Panda-Intelligence/panda-standard-board/hardware/thin18-compact/c4d9-96x68-aip-buffers/README.md

# Thin18 Compact C4D-9 — AIP74LVC2G17 EPD buffers

U801-U803 are changed to Wuxi I-core AIP74LVC2G17GC363.TR / C3294722 using the existing SOT-363 footprints and identical nets. Native ERC/DRC/parity are clean. Threshold/leakage/waveform qualification remains open.
