Panda-Intelligence/panda-standard-board/hardware/thin18-compact/core-c1-96x68-split/eda/core/PANDA-STD-CORE-EVT/PANDA-THIN16/models/README.md

# USB4500 model restoration

The STEP is the pinned KiCad Tiny Tapeout demo asset, Git blob
`cee214252a14ce383e84d3eaf1a94ca5bc54bab2`. Restore with the source tool
`restore_thin13_model.py`; the local delivery package includes it.
The donor demo licence is Apache-2.0 (LICENSE.txt). The model is a reference,
not independent manufacturer or worst-case tolerance approval.
