Panda-Intelligence/panda-standard-board/docs/design/key-calculations.md

# Panda 標準電子書板：WP4 關鍵計算清單

工作包：WP4（EVT 核心板原理圖）
日期：2026-08-11（USB／IRQ／BQ_PG差量同步：2026-09-08，Codex）
狀態：數據手冊計算 + 已提升USB／IRQ／BQ_PG工程候選；**不等於資格完成**。WP3官方模型／原廠EVM或受控bench仍無完整結論，WP3／WP4 pass與製造發布保持未關閉；保留`VFB`容差及§5／§6歷史取捨
適用板號：`PANDA-STD-CORE-EVT`

本文件承接 [power-datasheet-calculations.md](power-datasheet-calculations.md)（WP3）的 §12 傳遞項，補完
WP4 必辦計算，並新增充電輸入限流、超級電容與擴充器終端三項 WP4 專屬計算。凡 WP3 已算過者只作交叉引用與
必要重算，不重複抓取數據手冊。

2026-09-08 正式USB／IRQ／BQ_PG工程候選已提升（149封裝／1766段／306via，DRC0/0/0、ERC18）；共同證據見
[USB2 S-9 A-stage](lib/review/USB2-S9-A-stage.md)與[BQ_PG記錄](lib/review/BQ_PG-P10-A-stage.md)。本輪只同步相關差量；8月計算與取捨保留為歷史，
深睡還須計入未有界的PG專屬漏電；既有混合包絡見§4.5、總USB源電流門見§5.3.1，不以CAD檢查代替任何製造／台架資格。

---

## 0. 標記與新增假設

| 標記 | 意義 |
| --- | --- |
| **[手]** | 官方數據手冊值，可在文件號對應章節複核 |
| **[算]** | 由 **[手]** 值依本文件列出的算式推算 |
| **[估]** | 估算／規劃假設，未經實測，**不得**作為承諾 |

沿用 WP3 §0.1 的壓力情境 A1–A5（3.0／4.2 V 只作 TPS63802 VIN 情境，不是 `VSYS_RAW` rail bounds；
η=0.90、負載 0.70／1.00 A、f=1.4 MHz）。本文件新增：

| # | 假設 | 值 | 為何是假設 | 解除條件 |
| --- | --- | --- | --- | --- |
| A6 | 超級電容自漏電流 | **[估]** 1／5／10 µA 三檔並列 | 精確料號未選定；漏電是超級電容最大變異項，且與容量正相關 | WP4 選型取得25 °C／實際施加電壓下漏電及調理時間；額定電壓測試另列 |
| A7 | `VSYS_RAW` qualification bounds | **未凍結；4.5 V 僅作元件壓力點** | `SYS` 依 `VSYSMIN`、`VBAT`、source mode、system／charge load、DPM／thermal regulation、BATFET 與 dropout；不得先宣稱 fixed max | WP3 受控計算 + 官方模型模擬或 EVM／bench fallback |
| A8 | 快充目標輸入電流 | **[算]** 約 0.93 A + 系統併載 | 由 1 A 電池充電、4.2 V 電芯、5 V 輸入、η=0.90 推算 | 目標電芯與整機熱資格 |

---

## 1. `3V3_AON` 反饋分壓完整誤差（補齊 WP3 §5.4 缺失輸入）

### 1.1 補轉錄的 `VFB` 容差與模式邊界

WP3 §5.4 標記 `VFB` 容差**未轉錄**，導致 §5.3 誤差窗口不完整。WP4 已從 SLUSEB5B 電氣特性表補轉錄：

| 符號 | 參數 | 測試條件 | MIN | TYP | MAX | 單位 |
| --- | --- | --- | --- | --- | --- | --- |
| `VFB` | Feedback Regulation Voltage | — | — | 500 | — | mV |
| `VFB` | **Feedback Voltage accuracy** | **PWM mode** | **−1** | — | **+1** | **%** |
| `IFB` | Feedback Input Bias Current | VFB = 500 mV | — | 5 | 100 | nA |
| `VTHR;EN` | EN 腳上升門檻 | — | 1.07 | 1.1 | 1.13 | V |
| `VIH` | 高電平輸入電壓 | — | 1.2 | — | — | V |
| `VIL` | 低電平輸入電壓 | — | — | — | 0.4 | V |
| `tPG;delay` | Power Good 延遲 | `VFB` 下降 | — | 14 | — | µs |

⚠ **`VFB` 容差只在 PWM mode 下規範。** `IPWM/PFM` 1.06 A 的完整定義是「進入 PFM 的峰值電感電流」，
不是輸出負載電流。WP3 舊版把 0.70／1.00 A `IOUT` 直接與 1.06 A 比較，據此斷言全部正常負載為 PFM；
該推論已撤回。下列窗口只表示**資料手冊 PWM 條件**，不能套用到尚未判定模式的 automatic PWM/PFM 工作點，
也不能證明 PFM 直流精度。

### 1.2 PWM 規範條件下的三項疊加重算 **[算]**

```text
VOUT = VFB × (1 + R1/R2) + IFB × R1
```

R1 = 560 kΩ、R2 = 100 kΩ（WP3 §5.1 選項 F1，R2 為數據手冊上限 **[手]**）。

最壞高側：`VFB` 取 505 mV、R1 取上限、R2 取下限、`IFB` 取 100 nA
最壞低側：`VFB` 取 495 mV、R1 取下限、R2 取上限、`IFB` 取 0

| 電阻容差 | VOUT 最壞低 **[算]** | VOUT 最壞高 **[算]** | 對 3.6 V 上界餘裕 | 對 3.0 V 下界餘裕 |
| --- | --- | --- | --- | --- |
| ±1 % | 3.2076 V | **3.4467 V** | 0.1533 V | 0.2076 V |
| **±0.5 %（採用）** | **3.2394 V** | **3.4177 V** | **0.1823 V** | **0.2394 V** |
| ±0.25 % | 3.2554 V | 3.4033 V | 0.1967 V | 0.2554 V |

±0.5 % 的逐步代入 **[算]**：

```text
高側：R1 = 562.8 kΩ、R2 = 99.5 kΩ → R1/R2 = 5.656281 → (1+R1/R2) = 6.656281
      VFB 項 = 0.505 × 6.656281      = 3.361422 V
      IFB 項 = 100 nA × 562.8 kΩ     = 0.056280 V
      VOUT_max                       = 3.417702 V

低側：R1 = 557.2 kΩ、R2 = 100.5 kΩ → R1/R2 = 5.544279 → (1+R1/R2) = 6.544279
      VOUT_min = 0.495 × 6.544279    = 3.239418 V
```

### 1.3 與 WP3 §5.3 的差異與後果

| 項目 | WP3 §5.3（未含 `VFB` 容差） | WP4 本節（含 `VFB` ±1 %） | 變化 |
| --- | --- | --- | --- |
| VOUT 窗口（±0.5 %） | 3.2721 … 3.3844 V | **3.2394 … 3.4177 V** | 擴大 0.0663 V |
| 上側紋波預算 | 0.216 V | **0.1823 V** | **−15.6 %** |
| 下側紋波預算 | 0.272 V | **0.2394 V** | −12.0 % |

比對基準 **[手]**：ESP32-S3 `VDD3P3`／`VDD3P3_RTC`／`VDD3P3_CPU` 建議 3.0／3.3／3.6 V。

**判定：在 PWM 規範條件下，加入 `VFB` 容差後窗口仍完整落在 3.0–3.6 V 內，±0.5 % 電阻選擇可作 EVT
候選。** 0.1823 V／0.2394 V 只是該 PWM 算術窗口到絕對電壓邊界的距離；因 `VFB` accuracy 未規範 PFM，
**不得**把這兩個數字當 automatic/PFM 紋波預算或資格門。

不建議僅為增加 PWM 算術距離改用 ±0.25 % 電阻。正確關門方式是以 `MODE`=LOW／HIGH 分別掃 VIN、負載與
Wi-Fi/SD 工況，直接確認 `VOUT` 全時域維持 3.0–3.6 V；活動態 `MODE` 策略在該實測前保持未凍結。

### 1.4 分壓靜態電流（併入 §4）

```text
Idiv = VOUT / (R1 + R2) = 3.3 / 660 kΩ = 5.00 µA   [算]
```

R2 ≤ 100 kΩ 是數據手冊硬上限 **[手]**，故 5.00 µA 是此拓樸的**數學下限**（WP3 §7.2 已證），本文件沿用。

---

## 2. XFL4015 family reference candidate 峰值電流與飽和裕度情境（C2 後重算）

### 2.1 C2 決策的電感有效值窗口

WP3 §4.3 衝突一採 **C2：±20 %（或更緊）容差的 0.47 µH**，使有效值 **0.376–0.564 µH** 完整落入數據手冊建議
工作條件 0.37–0.57 µH **[手]**。IPEAK 的紋波項與 L 成反比，故最壞條件為 **L = 0.376 µH**。

### 2.2 式 (2) 代入（VIN = 3.0 V boost 壓力情境；不是已知最惡劣 rail bound） **[算]**

```text
IPEAK = Iout / (η × (1 − D))  +  (Vin × D) / (2 × f × L)
D = 0.0909、η = 0.90、f = 1.4 MHz、L = 0.376 µH

紋波項 = (3.0 × 0.0909) / (2 × 1.4e6 × 0.376e-6) = 0.2727 / 1.0528 = 0.2590 A
```

| Iout | DC 項 **[算]** | 紋波項 **[算]** | **IPEAK** **[算]** | ×1.2 數據手冊建議裕度 **[手]** |
| --- | --- | --- | --- | --- |
| 0.70 A **[假 A3]** | 0.8556 A | 0.2590 A | **1.1146 A** | 1.3375 A |
| 1.00 A **[假 A4]** | 1.2222 A | 0.2590 A | **1.4812 A** | 1.7774 A |
| 2.00 A 數據手冊上限 | 2.4444 A | 0.2590 A | **2.7034 A** | 3.2441 A |

### 2.3 對 TI 推薦表所列 Isat 5.4 A 與 `IPK` MIN 4 A 的情境裕度 **[算]**

| Iout | ×1.2 值 | vs Isat 5.4 A **[手]** | IPEAK | vs `IPK` MIN 4 A **[手]** |
| --- | --- | --- | --- | --- |
| 0.70 A | 1.3375 A | **4.04×** | 1.1146 A | **3.59×** |
| 1.00 A | 1.7774 A | **3.04×** | 1.4812 A | **2.70×** |
| 2.00 A | 3.2441 A | **1.66×** | 2.7034 A | **1.48×** |

**判定：C2 選定的 ±20 % 容差件在全負載範圍對 Isat 與 IC 限流都有裕度，無衝突。**
且 C2 比 WP3 表中用 −30 % 降額（L=0.329 µH、紋波 0.296 A）更寬鬆，證實 C2 是收緊而非放寬。

⚠ 沿用 WP3 §4.4 的殘留風險：Isat 5.4 A < `IPK` MAX 5.75 A **[手]**，故障暫態下電感可能先於 IC 限流飽和。
本節不改變該風險評級（已知殘留、非阻塞、列故障注入台架項）。

### 2.4 WP4 選型必辦（尚未關閉）

C2 只凍結**電氣容差要求**，不等於 TI 推薦表中的 `XFL4015-471ME` exact name 已合格。必辦：

1. 由供應商確認 exact suffix／orderable MPN 與 reel／packaging；
2. 取得該可訂購料號的**容差規格**，確認為 ±20 % 或更緊；
3. 取得**電流／溫度降額曲線**，確認在 §2.2 壓力情境與工作溫度下有效值仍 ≥0.37 µH；
4. 確認供應商的**飽和定義**與 supplier-controlled land pattern。

XFL4015 family body envelope 為 **4.0×4.0×1.5 mm**，但這不凍結 land pattern。**推薦表本身不構成上述任一項
驗證。** 全部資料取得前 `L401` 只可視為 family／reference candidate。

---

## 3. 有效電容降額驗算

數據手冊建議工作條件為**有效值** **[手]**；降額假設為電容 **+20 % / −50 %** **[手]**。

| 位置 | 數據手冊 MIN（有效） | 標稱 | 最壞降額有效值 **[算]** | 裕度 **[算]** | 判定 |
| --- | --- | --- | --- | --- | --- |
| `CO`（VOUT） | **7 µF** | 22 µF 單顆 | 11.0 µF | **1.57×** | ✅ |
| `CI`（VIN） | **4 µF** | 10 µF | 5.0 µF | **1.25×** | ⚠ 偏緊 |
| `CI`（若採 E2） | 4 µF | 22 µF | 11.0 µF | **2.75×** | ✅ |

### 3.1 `CI` 取捨結論：採 WP3 §8.2 的 E2

WP3 §8.2 列出 E1／E2／E3 三選項並未裁決。WP4 **採 E2：`CI` 改 22 µF / 6.3 V**，理由：

| 理由 | 說明 |
| --- | --- |
| 裕度由 1.25× 升至 2.75× | −50 % 是**通用**降額假設，未含本設計實際 DC bias、溫度與老化三項疊加 |
| DC bias 壓力條件 | `VSYS_RAW` 上界未凍結；4.5 V 只作 **[假 A7]** 壓力點。6.3 V 0603 X5R 在高偏置下容值跌落**可能超過 50 %**，須以 WP3 受控 max 重算 |
| 數據手冊明許 | 「輸入電容值可無限制增加」**[手]** |
| 佔位與成本代價低 | 同 0603 封裝，僅成本略增；ESR 維持 10 mΩ（不像 E1 升到 40 mΩ） |
| 組合合法性不變 | 0.47 µH + 10 µF 的非法組合限制**只針對 `CO`**（WP3 §8.1），`CI` 不受該表約束 |

**採 E2 後 §3 全部項目都有 ≥1.57× 裕度，`CI` 不再是最緊項。** 但 DC bias 曲線驗證**仍必辦**：E2 降低風險，
不消除驗證義務。

⚠ 原理圖與複核清單必須明確標注 `CI` 與 `CO` 的組合限制區分（WP3 §8.1 已警告此為易誤讀點），避免複核者
把 `CI` 判為非法組合。

### 3.2 bulk 電容判定

數據手冊 **[手]**：輸入源距 IC 超過數英寸需追加 bulk 電容（典型 47 µF 電解／鉭）。
`VSYS_RAW` 來自同板 BQ25628E，距離短 → **預期不需要**。此判定須在 WP7A 實際佈局距離確定後複核（WP3 §12 已列）。

---

## 4. 深睡靜態電流最終表（D1 決策後）

本表保留8月器件預算基線，僅USB／IRQ相關行加入當前覆蓋，不重新資格化其他器件；§4.2–4.3舊合計為
USB監控加入前的歷史推導，當前差量覆蓋見§4.5。

### 4.1 逐元件表

| 元件 | 狀態 | typ | max | 依據 |
| --- | --- | --- | --- | --- |
| ESP32-S3 | Deep-sleep，RTC memory + RTC 週邊上電 | **8.0 µA** | — | 晶片規格書 v2.2 表 5-10 **[手]** |
| TPS63802 | power save（`MODE`=LOW）、輕載 | **11 µA** | — | SLVSEU9D Iq **[手]** |
| BQ27427 | **SLEEP**（D1 已決策保留） | **9.0 µA** | — | SLUSEB5B §5.5 `ISLP` **[手]** |
| BQ25628E | battery-only、BATFET 開、**ADC 關** | **1.5 µA** | 3 µA | SLUSFA4C `IQ_BAT` **[手]** |
| TUSB320LI | VBUS-only，拔線後無主動電池供電；隔離／監控有限負載另列 | — | — | 非整接口零負載；S-9掉電／漏電仍待測 |
| USB隔離／監控 | 指定稳態工程預算 **3.8µA**，非typ/max器件規格 | — | — | §4.5條件假設；半掉電／ramp不在此保證 |
| TCA9535 #1 | standby、`fSCL`=0、no load | **0.9 µA** | 2.2／4 µA | SCPS201E（見 §4.3） **[手]** |
| RV-3028-C7 | 切換停用的歷史timekeeping例；I²C inactive、CLKOUT disabled、VDD=3 V/25°C、I/O在0或VDD | **0.045 µA** | 0.060 µA | 手冊p97 `IDD`（舊稿稱IDDO）；未來啟用LSM須改核`IDD:LSM`，不能沿用此列 |
| **`3V3_AON` FB 分壓** | 恆導通 | **5.00 µA** | — | §1.4 **[算]**（WP3 §7.1 首次發現） |
| **超級電容自漏電** | 涓流充飽後由 `3V3_AON` 持續補償 | **[估] 1–10 µA** | — | **§6 新發現，power-tree.md §5 未列** |
| LSM6DSO32X | power-down | **待實測** | — | 需按實際 ODR／量程複核 |
| 負載開關 ×4 | 關斷漏電 | **[估] <1 µA 合計** | — | 料號未定 |
| I²C／INT／KEY_POWER_MCU上拉 | 空閒高時理想電阻無壓差，接收器漏電仍計入 | ≈0（僅電阻本體） | — | §7.1，非整接口零負載 |
| TCA9535 P15備用終接 | 保留100k下拉；P16/P17為10k AON上拉CC輸入 | ≈0（僅P15電阻本體） | — | §7.3當前覆蓋 |
| BQ_PG／P10上拉 | R600=10k／1%至AON；battery-only釋放高態的PG專屬漏電未定 | 待驗 | 待驗 | 不能借INT/STAT界限；有效输入低態約0.33mA是另一供電狀態的電阻計算 |
| TUSB320 `EN_N` 網路 | 固定接GND；VBUS=0無本地上拉供電 | — | — | VBUS有效時耗流屬USB域，不能用舊「靠內部上拉停用」描述本候選 |
| MAX98357A `SD_MODE` 分壓 | `VSYS_AUDIO` 關斷 → 分壓源為 0 | **0** | — | §7.3 |

### 4.2 歷史合計與判定（USB監控加入前） **[算]**

```text
已知固定項（不含超級電容、IMU、開關漏電）：
  8.0 + 11 + 9.0 + 1.5 + 0 + 0.9 + 0.045 + 5.00 = 35.445 µA

+ 超級電容漏電 1 µA  [估]  → 36.45 µA
+ 超級電容漏電 5 µA  [估]  → 40.45 µA
+ 超級電容漏電 10 µA [估]  → 45.45 µA
```

| 情境 | 合計 **[算]** | vs 50 µA 上限（D1 基準） | 餘裕 |
| --- | --- | --- | --- |
| 超級電容漏電 1 µA | 36.45 µA | 計算包絡內 | **13.55 µA** |
| 超級電容漏電 5 µA | 40.45 µA | 計算包絡內 | **9.55 µA** |
| 超級電容漏電 10 µA | 45.45 µA | 偏緊 | **4.55 µA** |

**上述餘裕尚須容納 LSM6DSO32X power-down 與 4 顆負載開關漏電（合計 <1 µA **[估]**）。**

### 4.3 ⚠ 歷史：對 D1「餘 13.60 µA」的修正

D1 決策記錄曾稱「50 µA 上限仍餘 13.60 µA」，但漏了超級電容；上一版又錯把 VBUS-only TUSB320LI 的
1.7 µA shutdown max 加入電池深睡。兩項一併修正後，採 S1 漏電 1–5 µA 時的計算餘裕為 **9.55–13.55 µA**。

**這不推翻 D1，也不構成通過**：IMU power-down、四顆負載開關、板面污染與溫度仍未實測。超級電容漏電仍是
關鍵選型參數；10 µA 級只餘 4.55 µA，不得在其餘漏電未知時採用。

→ **超級電容選型準則S1：25 °C、實際施加電壓下漏電 ≤5 µA**（見 §6.4）；額定電壓或不同調理時間的資料不得混同。

### 4.4 ✅ 反面查核：TCA9535 standby 測試條件（關閉 WP3 §7.4 疑慮）

WP3 §7.4 標記「0.9 µA typ 的測試條件（VCC=3.6 V、輸入接地）與本設計實際狀態不符」，因本設計深睡時多路
擴充器輸入為 HIGH。WP4 回查 SCPS201E 電氣特性表，發現數據手冊給出**兩組**測試條件：

| 測試條件 | VCC | typ | max |
| --- | --- | --- | --- |
| **VI = VCC**（輸入全高）、IO = 0、I/O = inputs、`fSCL` = 0 kHz、no load | 3.6 V | **0.9 µA** | **2.2 µA** |
| **VI = GND**（輸入全低）、IO = 0、I/O = inputs、`fSCL` = 0 kHz、no load | 3.6 V | **0.9 µA** | **4 µA** |

**兩個包絡條件的 typ 都是 0.9 µA。** 本設計輸入為高低混合，必然落在兩者之間。

**判定：WP3 §7.4 的疑慮解除。0.9 µA typ 適用；max 以較差者 4 µA 為界。**
⚠ 但兩列條件都註明 `I/O = inputs`，而本設計 P00–P03／P05 為**輸出**（當前P10已保留輸入）。深睡時這些輸出的電位已在
§7.2／§7.3 逐一確認為不產生電流，故仍適用；WP9 實測依舊必要（power-tree.md §5 已列）。

**來源編號更正已同步**：舊版曾誤記 TCA9535 文件號。官方下載文件頁眉為
**SCPS201E – AUGUST 2009 – REVISED MAY 2022**；目前受控文件一律使用 SCPS201E。此更正不改變電氣結論。

### 4.5 2026-09-08 USB差量包絡（不是整板max保證）

條件為VBUS=0、AON有效、CC rail已穩定放電：AUP2G07雙路保守2.4µA + AUP1G17輸入0.5µA + ICC0.9µA =
**3.8µA**。2.4µA含Ioff與ΔIoff保守相加假設，不是廠家全狀態新保證；0.2–0.8V及ramp另測。
47k+1%=47.47k泄放在2.9µA假設注入下約0.1377V，不能據此證明全衰減過程受控。

```text
舊已知typ／估算固定項35.445µA + USB指定穩態预算3.8µA = 39.245µA
+ 超級電容估算1 / 5 / 10µA → 40.245 / 44.245 / 49.245µA
對50µA名義餘量             →  9.755 /  5.755 /  0.755µA
```

採1–5µA超級電容假設，當前混合工程包絡四捨五入 **40.25–44.25µA**，餘量 **5.75–9.75µA**。
這混合typ、估算與部分保守器件預算，**不是整板最壞電流，也未通過50µA門**。超級電容尚未實現，
IMU、開關、板漏、溫度、實際DC狀態和過渡仍未完成。不得把舊舍入數重複累加或將3.8µA當typ規格。

---

## 5. 🔴 新衝突一：500 mA 硬體默認與 1 A 電池充電互斥

### 5.1 BQ25628E 輸入限流的兩個來源

| 來源 | 機制 | POR 預設 | 復位條件 | 依據（SLUSFA4C **[手]**） |
| --- | --- | --- | --- | --- |
| `ILIM` 腳（硬體） | `IINREG = KILIM / RILIM`，`RILIM` 接地 | 由電阻決定，**與韌體無關** | 不適用（硬體） | §6 腳位表、§7.5 |
| `IINDPM` 暫存器（韌體） | REG0x06/07 | **3200 mA（A0h）** | `REG_RESET`；**移除轉接器時重置回 3.2 A** | REG0x06 欄位表 |
| `EN_EXTILIM` | =0 時**停用 `ILIM` 腳** | **1h（啟用）** | `REG_RESET`、**`WATCHDOG`** | REG0x15 bit 2 |
| `ICHG`（電池充電電流） | REG0x02/03 | **320 mA（8h）**，範圍 40–2000 mA | `REG_RESET`；watchdog 逾時設為前值 **1/2** | REG0x02 欄位表 |

實際輸入限流 = `ILIM` 腳與 `IINDPM` **兩者取小** **[手]**。

### 5.2 ⚠ 關鍵推論：`IINDPM` 無法提供安全默認

`IINDPM` 的 POR 值是 **3200 mA**，且**移除轉接器時自動重置回 3.2 A**。因此：

> PRD 的默認≤500mA總門不能靠暫存器POR值關閉；BQ分支須由`ILIM`電阻提供默認限制，另須給繞過BQ的USB旁路留出預算。

這使 `RILIM` 從「可選的額外保護」升級為**必裝且不可省的安全元件**。既有文件（power-tree.md §7、
i2c-address-map.md）未記錄 `ILIM` 腳與 `RILIM`，WP4 於此補齊並列為原理圖必辦項。

### 5.3 `RILIM` 計算（500 mA 硬體默認） **[算]**

`KILIM` = 2250 / 2500 / 2750 AΩ（MIN/TYP/MAX，測試條件 **INREG = 1.6 A**） **[手]**。
最壞高電流 = `KILIM` 取 MAX、`RILIM` 取下限：

```text
RILIM_min ≥ KILIM_max / 0.5 A = 2750 / 0.5 = 5500 Ω
E24 取 5.6 kΩ ±1 % → 5544 … 5656 Ω

IINREG 外推高 = 2750 / 5544 = 0.4960 A   （僅BQ分支，不是總USB門通過）
IINREG 最壞低 = 2250 / 5656 = 0.3979 A
→ 輸入限流窗口 398 … 496 mA
```

**判定邊界：5.6 kΩ ±1 % 產生 398–496 mA 是把 `KILIM` 的 1.6 A 規範外推到 0.4–0.5 A 的計算窗口，
不是資料手冊保證窗口，也不能單憑此式宣稱 PRD 硬體默認已合格。**

此外，SLUSFA4C §8.3.3.3 明文要求：ILIM 設定**低於 400 mA**時，須在 `RILIM` 並聯一條 **1.2 kΩ + 330 nF
串聯 RC** 支路。計算窗口低端 397.9 mA 已跨過 400 mA，因此 EVT 原理圖必須裝此 RC；缺任一元件即阻塞
輸入限流門。WP9須在J201量測上電、穩態、拔插、弱源與溫度下的**總源電流**，含全部旁路，≤500mA才可關門。

### 5.3.1 2026-09-08 總USB源電流邊界（仍未通過）

```text
I_USB_source = I_BQ_input + I_R209 + I_LDO_input + I_VBUS_divider + I_TUSB_VBUS_DET + 其他入口漏電／動態充電
I_R209(5.5V, -1%) = 5.5V / 990Ω = 5.5556mA
R209功耗 = 5.5² / 990Ω = 30.5556mW（0603，要求≥0.1W）
原KILIM外推上端 = 2750 / 5544 = 496.0317mA（僅BQ分支，且非此工作點保證規格）
只相加上述兩項 = 501.5873mA，尚未計CC／LDO／monitor
```

此式證明**原預算不足以關閉總門**，不表示任意實板必然一直超500mA。本輪不改R201，不能只把BQ支路設為500mA
就宣稱整機合格。CC rail內47k泄放約70.2µA、4.7k OUT1/2低態各約0.702mA、OUTA上拉／下拉及IC耗流屬
`I_LDO_input`的內部分解，不能再在LDO輸入之外重複相加。較高CC源能力也須連同電芯／NTC／熱與總源預算實測。

直接VBUS電容C202/C209各1µF，共2µF nominal；CC rail C210=2.2µF與C211/C212/C213各0.1µF，共2.5µF。
六顆4.5µF，統一+20%=5.4µF，按5.5V為29.7µC；非全系統inrush保證，C215/TVS寄生、BQ啟動至PMID/SYS及
實際插拔仍待測。C214屬AON不重複加；C210的exact MPN須在3.3V、全容差／溫度／DC-bias後有效≥1.5µF。

### 5.4 衝突：1 A 電池充電需要約 2 倍於該上限的輸入電流 **[算]**

```text
電池側功率  = 1.0 A × 4.2 V              = 4.20 W
輸入側功率  = 4.20 / 0.90 [假 A2]        = 4.67 W
5 V 輸入電流 = 4.67 / 5                   = 0.933 A   [假 A8]
再加系統併載（MCU + SD + 顯示邏輯）      → 更高
```

反推：在 `ILIM` 固定 5.6 kΩ、`EN_EXTILIM`=1 的條件下可達的最大電池充電電流：

| 輸入限流 | 輸入功率 | ×0.90 | @4.2 V 電芯 | @3.7 V 電芯 |
| --- | --- | --- | --- | --- |
| 0.398 A（最壞低） | 1.99 W | 1.79 W | **0.426 A** | 0.484 A |
| 0.496 A（最壞高） | 2.48 W | 2.23 W | **0.531 A** | 0.604 A |

**且上表尚未扣除系統併載。**

> 🔴 **衝突：`RILIM` 若恆定為 500 mA 級，電池充電電流上限約 0.43–0.60 A，PRD 已凍結的「最高 1 A 電池充電」
> 在物理上不可達。**

### 5.5 歷史L1／L3取捨選項（當前總源門由§5.3.1覆蓋）

| 選項 | 作法 | 優點 | 代價／風險 | 判定 |
| --- | --- | --- | --- | --- |
| **L1** | `RILIM` = 5.6 kΩ 恆在；資格通過後韌體寫 `EN_EXTILIM`=0 **停用 `ILIM` 腳**，改由 `IINDPM` 控制 | 零額外元件；POR為BQ分支500mA級外推候選，非總源門通過；WATCHDOG可恢復EN_EXTILIM=1 | 快充期間硬體夾制**不存在**；見§5.6拔插風險與§5.3.1總源門 | 歷史EVT基線，資格未關 |
| L2 | `RILIM` 直接按快充上限（1.2 A → 2.32 kΩ）設定，500 mA 默認交由韌體寫 `IINDPM` | 硬體夾制恆在且無需切換 | ❌ `IINDPM` POR = 3.2 A，POR 到韌體寫入之間有最高約 1.2 A 的開窗；**違反 PRD 硬體默認要求** | ❌ 不採 |
| **L3** | `RILIM` = 5.6 kΩ 恆在，並聯一顆 4.02 kΩ 經 MOSFET 由擴充器 P15 切入；閘極下拉 → 預設關斷 | 硬體夾制不消失，可刻意抬升約0.96–1.17A；POR仍只是BQ分支500mA級外推 | +1 MOSFET/+1電阻、佔P15；切回需韌體紀律 | 歷史DNP退路；本批未新增此電路，P15仍預留 |

L3 併聯值 **[算]**：

```text
目標快充上限約 1.2 A → R_par ≥ 2750 / 1.2 = 2292 Ω
5.6 kΩ ∥ Rx = 2292 → Rx ≈ 3880 Ω → E96 取 4.02 kΩ ±1 %

最壞低 R_par = 5544 ∥ 4060 = 2343.7 Ω → IINREG 最壞高 = 2750 / 2343.7 = 1.173 A
最壞高 R_par = 5656 ∥ 3980 = 2336.3 Ω → IINREG 最壞低 = 2250 / 2336.3 = 0.963 A
→ 快充輸入窗口 0.963 … 1.173 A（≥0.933 A 需求 ✅）
```

### 5.6 ⚠ L1 的拔插不對稱風險（必須寫入韌體契約與 WP9 測試）

對照 §5.1 的復位條件表：

| 暫存器／位 | 移除轉接器時是否復位 |
| --- | --- |
| `IINDPM` | **是**，重置回 3.2 A **[手]** |
| `EN_EXTILIM` | **否**（只由 `REG_RESET` 與 `WATCHDOG` 復位） **[手]** |

危險序列：

```text
1. 接上合格 1.5 A 源 → 韌體寫 EN_EXTILIM=0、IINDPM=1.2 A → 快充
2. 使用者拔線          → IINDPM 自動重置 3.2 A；EN_EXTILIM 仍為 0（ILIM 腳仍停用）
3. 立即插入弱 500 mA 源 → 硬體夾制不存在、IINDPM=3.2 A
                        → 在韌體重新偵測並改寫前，充電器可能嘗試遠超源端能力的輸入電流
```

`VINDPM`（輸入電壓 DPM）會依 VBUS 塌陷回折電流，這是設計內的保護；但**開窗真實存在**。

**韌體契約（硬體通過的必要條件）**：

1. `EN_EXTILIM`=1 是**靜止狀態**。只有在「GPIO2有效 + TUSB320LI初始化／CC狀態穩定 + 電芯／NTC／熱及總源預算合格」
   全部成立期間才可置 0；
2. GPIO2下降直接撤銷USB／快充資格，合併CC／charger事件後**立即**恢復`EN_EXTILIM=1`並核限流；不能只靠TCA輪詢／EXP_INT。GPIO响应不证明模拟3ms或ROM階段已受控；
3. 充電器 watchdog **必須啟用**，作為韌體失效時恢復硬體夾制的最後防線；
4. 上述三項列入 WP9 台架強制項，含「快充中拔線後立刻換插弱源」的故障注入案例。

### 5.7 建議

**歷史建議**：採L1為EVT基線，以DNP保留L3（4.02kΩ + MOSFET + P15）退路。本批未新增L3，P15僅預留。

歷史理由：L1零額外器件且有watchdog退路；當前不能据此關閉PRD默認總源≤500mA（見§5.3.1）。§5.6開窗仍依賴韌體
紀律關閉，屬**軟體依賴的安全性**。DNP 預留 L3 使 WP9 若判定 L1 不可接受時，**不需要重投一版核心板**即可切換。
這與 PRD 路線 B（能力／裕量優先）一致，且成本僅兩顆 DNP 元件。

⚠ **邊界宣告**：本節不宣稱任何充電安全性已合格。500 mA 與 1 A 都必須在目標電芯、`TS`／JEITA 設定、連接器與
整機熱資格通過後才成立；本節只證明**兩者不能由同一個固定 `RILIM` 同時滿足**，並給出取捨。

---

## 6. 🔴 新衝突二：RTC 超級電容漏電未計入深睡預算 + 容量估算

### 6.1 充電路徑與可用電壓窗口

2026-09-08 correction (Codex): use [RV-3028-C7 Application Manual Rev1.4](https://www.microcrystal.com/fileadmin/Media/Products/RTC/App.Manual/RV-3028-C7_App-Manual.pdf) pp97–99 for the configured LSM backup path.
The charge-ready voltage and full discharge-current envelope are not yet qualified; the following1.87V window is an
illustrative assumption, not a guaranteed minimum. 中文說明：不改24h/LSM或S1–S6，只撤回未有依據的最壞值說法。

RV-3028-C7 涓流充電器結構 **[手]**（應用手冊 §4.3）：`VDD` → 使能開關（`TCE`）→ **Schottky 二極體（典型
壓降 0.25 V）** → 串聯限流電阻（`TCR` 可選 3／5／9／15 kΩ）→ `VBACKUP`。

```text
V_backup(充飽) = VDD − V_Schottky − I_leak × R_TCR                       [算]

以 §1.2 靜態 VDD 低角點 3.2394 V、名義 R_TCR = 3 kΩ、假設 I_leak = 5 µA：
V_backup = 3.2394 − 0.25 − 0.015 = 2.974 V  →  此模型約 2.97 V，非下界
```

計時最低工作電壓 **[手]**：操作表的 `VBACKUP` MIN=1.1V。LSM最壞切入門檻2.2V不是保持截止電壓；
p99斷開VDD後的典型曲線向約1V延續，但典型曲線不能替代全放電範圍的最壞電流保證。

```text
演算假設 ΔV = 2.97 − 1.1 = 1.87 V（須以實際合格V_ready取代）              [算]
```

### 6.2 24 小時保時所需容量 **[算]**

```text
C = I_total × t / ΔV，t = 24 h = 86 400 s，ΔV = 1.87 V
```

LSM後備電流 **[手]**：手冊p97 `IBACKUP:LSM` 最大180nA，該行條件為VBACKUP=3.0V、TA=25°C、VDD<VTH:LSM（表列2.0V）；不能使用切換停用的`IDD`60nA（舊稿稱IDDO）。
該行未另列TCE條件，不補造設定；p99典型曲線明示I²C inactive、CLKOUT disabled及VDD=0V（先關閉VDD），不能把圖的條件/典型值當成新增最大值規格。
下面暫把180nA當定電流做條件演算，不宣稱這是1.1V至V_ready全範圍的已驗界限。
PCB 漏電估 **[估]** 0.1 µA（短網路、清潔板面）。

| 情境 | 超級電容自漏電 **[估 A6]** | `I_total` | **所需 C** **[算]** |
| --- | --- | --- | --- |
| 僅 RTC 的條件例（忽略電容與 PCB 漏電） | 0 | 0.18 µA | **8.32 mF** |
| 低漏電件假設 | 1 µA | 1.28 µA | **59.14 mF** |
| 中漏電件假設 | 5 µA | 5.28 µA | **243.95 mF** |
| 高漏電件假設 | 10 µA | 10.28 µA | **474.97 mF** |

### 6.3 ⚠ 自我參照效應

超級電容漏電**與容量正相關**：加大容量以覆蓋漏電，會同時提高漏電，需要更大容量。因此 §6.2 不是可以直接
取值的設計表，而是**選型收斂條件**：必須以候選料號的實際漏電規格代入，反覆驗證直到自洽。

```text
條件模型：C_effective_min ≥ (I_RTC + I_PCB + I_leak) × 86400 / ΔV_verified
```

**本文件不凍結任何電容值。** §6.2 的四列是包絡示範，不是候選規格。

### 6.4 對深睡預算的影響（power-tree.md §5 未列的項）

涓流充電器充飽後，超級電容的漏電**由 `3V3_AON` 持續補償**，因此它是常態深睡負載。
[power-tree.md](power-tree.md) §5 的舊版元件表曾漏此行；本輪已同步更正。D1 的原始「餘 13.60 µA」
不能直接沿用。USB加入前、採S1漏電1–5µA的歷史餘裕為§4.2／§4.3的 **9.55–13.55µA**；
當前再加USB指定稳態差量後為§4.5的 **5.75–9.75µA**，仍未扣IMU／開關／板級未知項。

→ **超級電容選型準則（WP4 凍結為硬性項）**：

| # | 準則 | 值 | 理由 |
| --- | --- | --- | --- |
| S1 | 25 °C、實際施加電壓下漏電 | **≤5 µA** | 10µA級歷史餘4.55µA；當前§4.5混合預算只餘0.755µA，IMU／開關未知時不可據此採用 |
| S2 | 額定電壓 | **≥3.3 V** | 保留篩選門；仍須核實實際最大充電電壓，不能扣除typ二極體壓降當保證。2.7V不符本門 |
| S3 | 有效容量（含容差、溫度、老化） | 滿足 §6.3 自洽條件 | 標稱值不等於壽命末期有效值 |
| S4 | 元件工作溫度 | 至少 −20…+60 °C（2026-09-11 使用者決定放寬；原值 −40…+85 °C） | 元件能力。放寬係為採用 RTC 後備候選 CPH3225A（原廠目錄 −20…+60 °C）。**後果**：低於 −20 °C 或高於 +60 °C 時 RTC 後備不保證；Rev A 整機仍受 N16R8 baseline +65 °C 限制 |
| S5 | 滿充時間 | 見 §6.5，需可納入產線節拍 | 實際初始狀態/調理條件與達指定V_ready時間待驗；不得把EDLC零初壓模型套用LIC |
| S6 | 類型 | 只允許經批准的可充電 supercapacitor／LIC | 一次性與可充電 coin battery 均排除；exact part／package blocked |

### 6.5 滿充時間 **[算]**

`TCR` 預設 3 kΩ **[手]**（EEPROM 37h 出廠值）。以一階 RC 估算：

The p98 electrical table gives2–4kΩ for that setting at VDD=5V/VBACKUP=3V, including the diode.
Do not combine this effective-path range with an independent0.25V diode corner and count the drop twice.
The table below is nominal linear RC planning only; actual time to a specified V_ready must be measured.
以下從0V起算僅是EDLC示例，並非所有器件的交貨狀態；LIC必須另核允許初始/最低放電電壓。

| C | τ = R×C（3 kΩ） | 3τ（約 95 %） | 5τ（約 99 %） |
| --- | --- | --- | --- |
| 50 mF | 150 s | 7.5 min | 12.5 min |
| 100 mF | 300 s | 15 min | 25 min |
| 250 mF | 750 s | 37.5 min | 62.5 min |
| 470 mF | 1410 s | 70.5 min | 118 min |

啟動突入電流（`V_backup` = 0 時） **[算]**：

```text
I_inrush = (3.3 − 0.25) / 3000 = 1.02 mA
```

此1.02mA是名義模型，不是突入或充電時間保證。**維持既定 `TCR` = 3 kΩ 檔位**，
但不以名義15mV電阻壓降推導最小充電完成電壓；本輪不另加充電器或軟啟動架構。

### 6.6 ⚠ EEPROM 出廠預設會使後備功能完全不工作

RV-3028-C7 的兩個關鍵設定都在 **EEPROM 37h**，且出廠預設為**停用** **[手]**：

| 欄位 | 出廠預設 | 本設計需要 |
| --- | --- | --- |
| `TCE`（涓流充電使能） | **停用** | **啟用** |
| `TCR`（串聯電阻） | 00 = 3 kΩ | 00 = 3 kΩ（維持） |
| `BSM`（後備切換模式） | **00 = 切換停用** | **11 = LSM**（見 §6.7） |
| `FEDE`（快邊緣偵測） | 1（已啟用） | 維持 1 |

→ **產線／bring-up 必辦**：出廠或首次上電必須寫入 EEPROM 37h。若略過，超級電容既不會充電、也不會在主電池
斷開時接手，**24 小時保時直接失效**且無任何硬體徵兆。此項列入 WP9 與產線治具強制檢查。

另有兩個未用腳契約：`EVI` 不得浮空，本設計以 10 kΩ 上拉至 RTC VDD；`CLKOUT` 可物理 no-connect，但 EEPROM
35h 出廠預設 `CLKOE=1`、32.768 kHz，故產線必須寫 `CLKOE=0` 且 `CLKF=0`（或 `FD=111`）並讀回。只放 no-connect
marker 而不禁輸出不算關閉未用腳。

⚠ 順序約束 **[手]**：讀寫 EEPROM 前必須先把 `BSM` 設為 00 或 10（停用切換），寫完再設回 11。

### 6.7 後備切換模式選擇：LSM（`BSM` = 11）

| 模式 | 切換條件 **[手]** | 判定 |
| --- | --- | --- |
| DSM（`BSM`=01） | `VDD` < `VBACKUP`；實際後備電壓未定 | 不採用，保留既定選擇 |
| **LSM（`BSM`=11）** | `VTH:LSM` 為1.8–2.2V（typ2.0）；初始後備電壓須滿足切入條件 | ✅ **維持採用，充電就緒前提待驗** |

**原選擇理由的條件邊界 [算]**：舊模型假設VBACKUP約2.97V、AON下衝至約3.00V，僅約30mV餘量，
因此選LSM避免接近後備電壓時的切換風險。這不是已量得的瞬態或必然誤切換；本輪維持LSM，不由典型值重選模式。

必須實測充電就緒電壓高於最壞LSM切入門檻，不能假設一定已滿充2.97V。2.2V是切入界限，**不是保持截止**；
可用擺幅須由實際V_ready、操作下限與負載範圍驗證，不能以模式名稱宣稱24h或完整電壓窗口已合格。

附帶 **[手]**：切回 `VDD` 時有 `tDEB` 122–183 µs 去抖；後備態下 `INT` 仍可輸出、I²C 自動停用並復位、
`CLKOUT` 拉低。這是RTC器件能力；當前板经共享EXP_INT/GPIO4通知，不是獨立GPIO2路徑。AON失電時能否喚醒MCU
須按實際供電狀態驗證，不能由RTC仍可輸出INT推導整板喚醒成立。

### 6.8 保時精度不是本節的門

**[手]** 時間精度 ±1 ppm @25 °C、首年老化 ±3 ppm。24 小時內 ±1 ppm ≈ **±0.086 s** **[算]**。
→ 24 小時要求是**保持不斷電計時**，不是精度要求；精度餘裕充足，兩者不得混談。

---

## 7. 終端與上下拉計算

### 7.1 上拉在深睡的電流貢獻

理想open-drain上拉電阻空閒高時無壓差；接收器／隔離器有限漏電仍須計，拉低時電阻耗流 **[算]**：

| 網路 | 建議阻值 | 拉低時電流 **[算]** | 深睡（空閒高）貢獻 |
| --- | --- | --- | --- |
| `EXP_INT`（含RTC） | R502=100k；R305 DNP | 33µA | 高態僅有限漏電；不把兩100k並為50k |
| `KEY_POWER_MCU` | R528=10k | 330µA（按下時） | 高態僅有限漏電 |
| CC_OUT1_AON／CC_OUT2_AON | R602/R603各10k | 各330µA | 低態為USB工作狀態，不是拔線稳態预算 |
| `PG_3V3_MAIN` | 100 kΩ | 33 µA（故障時） | ≈0（WP3 §7.5 已證） |
| `I2C_SCL`／`SDA` | 見 §7.4 | 依阻值 | ≈0 |

**判定**：理想電阻本體高態無壓差，不代表整接口零負載；接收器與隔離器漏電仍計入§4.5，不能全部忽略。

### 7.2 `EXP_INT` 阻值選擇：100 kΩ（偏離數據手冊建議值，附理由）

TCA9535 數據手冊建議 `INT` 上拉「典型約 10 kΩ」**[手]**（SCPS201E §7.3.3）。WP4 建議 **100 kΩ**：

| 考量 | 10 kΩ | 100 kΩ | 判定 |
| --- | --- | --- | --- |
| 拉低電流 **[算]** | 330 µA | 33 µA | 100 kΩ 優 |
| 上升緣 | 快 | 慢10× | 無USB資料速率要求，但RTC/TCA/跨板RC釋放及重入睡時序必須實測 |
| 匯流排電容 | 跨板間連接器 + 轉接板 wired-OR，電容較高 | 同 | 須以實測上升緣定案 |
| 誤觸發抗擾 | 較好 | 需含新增RTC與跨板負載實測 | 不以短網路估算關門 |

**偏離理由：`EXP_INT` 在按鍵持續按住或觸控持續中斷時會長時間為低，10 kΩ 的 330 µA 是不必要的耗流。**
這是歷史的電流優先取捨，不代表沒有上升緣／重入睡時序約束。當前新增RTC共享負載，R502為唯一已裝核心上拉、
R305 DNP；跨板容量、洩漏與清源後釋放需重測。

⚠ 這是**必須寫入 ERC／設計審查例外記錄**的偏離項（見 [schematic-spec.md](schematic-spec.md) 各頁例外表）。
實際阻值以 bring-up 實測上升緣定案，佈局預留 0402 可換件。

### 7.3 ⚠ TCA9535 空置埠必須終接（gpio-budget.md §7 未列）

SCPS201E 引腳表註腳 **[手]**：

> 「If port is unused, it must be tied to either VCC or GND through a resistor of moderate value (about 10 kΩ)」

**歷史（2026-08-11）**：[gpio-budget.md](gpio-budget.md) 當時將P15/P16/P17列備用且未終接，以下保留問題與取捨；
當前P16/P17接法由本節末尾覆蓋。當時的空置輸入不符合數據手冊要求：

- POR 時全部埠為**輸入**（SCPS201E 引腳表 **[手]**）；
- P 埠**無內部上下拉**（gpio-budget.md §7 已載明）；
- 浮空 CMOS 輸入會產生貫穿電流，直接影響 §4 的深睡預算。

**WP4 修正：P15／P16／P17 各加 100 kΩ 下拉至 GND。**

| 狀態 | 電流 **[算]** |
| --- | --- |
| 埠為輸入（POR 與深睡預設） | ≈0（僅 ±1 µA max 漏電，已含在 TCA9535 項） |
| 埠誤設為輸出並驅動高 | 33 µA／支 |

偏離數據手冊「約 10 kΩ」的理由：10 kΩ 在誤設為輸出驅動高時為 330 µA／支；100 kΩ 已足以定義 CMOS 輸入電平，
且保留 EVT 飛線用途。**韌體契約：深睡時 P15–P17 必須維持為輸入。**

**2026-09-08 覆蓋**：P16/P17不再備用，由R602/R603=10k上拉AON，作CC_OUT1/2輸入，移除其舊100k下拉；
P15仍保留原100k備用下拉；Fix23將P10/R600改為BQ_PG的10k／1% AON上拉。這些輸入不得誤配置推挽輸出，P15仍是未實作L3退路，不因歷史段落視為已裝。

Assuming near-zero BQ_PG low voltage, R600 current calculates to0.330mA at3.3V, or0.364mA at3.6V with−1% resistance. This is an AON resistor-load
calculation, not a PG VOL guarantee or a complete USB input-current budget. PG-specific high/off-state leakage is not
bounded by the INT/STAT table; keep sleep/current/back-power qualification open. 中文說明：不把釋放高態的上拉視為字面零漏電；見[BQ_PG記錄](lib/review/BQ_PG-P10-A-stage.md)。

### 7.4 I²C 上拉阻值的器件級約束（新增輸入）

[i2c-address-map.md](i2c-address-map.md) §5.2 未凍結阻值（等匯流排電容）。WP4 補上一條**器件級上界**
**[手]**（SLUSEB5B Table 7-1，BQ27427 建議值）：

| `VPU` | 建議範圍 | 典型（假設匯流排電容 10 pF） |
| --- | --- | --- |
| 1.8 V | 400 Ω ≤ `RPU` ≤ 37.6 kΩ | 10 kΩ |
| **3.3 V** | **900 Ω ≤ `RPU` ≤ 29.2 kΩ** | 5.1 kΩ |

⚠ 該典型值假設**匯流排電容 10 pF**，而本設計跨板間連接器與 FPC，實際電容遠高於 10 pF。故 5.1 kΩ 不可直接
採用為結論，只作**上界約束**：`RPU` ≤ 29.2 kΩ。這使 i2c-address-map.md §5.2 的未凍結範圍收窄為
**約 2.2 – 10 kΩ**（下界由深睡耗流與驅動能力決定，上界由本節與實測上升緣決定）。

### 7.5 ⚠ BQ27427 I²C 浮空防護（新增必辦，既有文件未列）

SLUSEB5B §7.4.1 佈局指引 **[手]**：

> 「Use external 1 MΩ pulldown resistors to VSS to avoid floating inputs to the I2C engine if the external
> pullup resistors on the SCL and SDA lines disconnect from the host during low-power operation.」

本設計 I²C 上拉在 `3V3_AON`（常供域），正常運作中**不會**與主機斷開，故該情境不成立。
**但 ship mode（BATFET 斷開）時 `3V3_AON` 消失，而 BQ27427 由 `BAT` 直供仍上電** → 此時 SCL／SDA 上拉消失，
BQ27427 的 I²C 引擎輸入浮空，正是數據手冊警告的情境。

→ **WP4 決定：加 1 MΩ 下拉至 VSS 於 `I2C_SCL` 與 `I2C_SDA`。**
深睡貢獻 **[算]**：匯流排空閒為高時 3.3 V / 1 MΩ = **3.3 µA／條 = 6.6 µA 合計**。

⚠ **這是 §4 未計入的第二筆新增電流。** 重算 §4.2：

```text
35.445 + 超級電容 1 µA + I²C 1 MΩ 下拉 6.6 µA = 43.05 µA   → 餘 6.95 µA
35.445 + 超級電容 5 µA + I²C 1 MΩ 下拉 6.6 µA = 47.05 µA   → 餘 2.95 µA ⚠
```

**判定：兩筆新增疊加後 50 µA 餘裕過薄。取捨如下（WP4 建議，非凍結）：**

| 選項 | 作法 | 深睡代價 | 風險 |
| --- | --- | --- | --- |
| **P1（建議）** | 只在 BQ27427 **本地**加 1 MΩ 下拉，且**改為 DNP**，EVT 先不裝 | 0 µA | ship mode 期間 BQ27427 I²C 輸入浮空；但 ship mode 是工廠運輸態，不要求燃料計精度，且退出 ship mode 後 `3V3_AON` 恢復。**列入 WP9 觀測項** |
| P2 | 裝 1 MΩ 下拉 | 6.6 µA | 侵蝕約半數剩餘餘裕 |
| P3 | 改 4.7 MΩ 下拉 | 1.4 µA | 抗浮空效果減弱，數據手冊只給 1 MΩ |

**建議 P1**：以 DNP 焊位保留能力，EVT 實測 ship mode 進出與 I²C 恢復；若觀察到異常再裝件。
這符合「EVT 保留調試位、裝配狀態由驗證決定」的既有原則（design.md §8）。

### 7.6 BQ27427 `BIN` 腳終接 **[手]**

SLUSEB5B §7.4.1：

- 「If the battery pack thermistor is not connected to the BIN pin, pull down the BIN pin to VSS with a 10 kΩ resistor.」
- 「**Do not directly short the BIN pin to VDD or VSS.**」

本設計電池包含 `NTC`（PRD 已凍結至少三線）。`BIN` 的接法取決於 NTC 由**充電器 `TS`** 或**燃料計 `BIN`** 使用，
或兩者分壓共用 —— 這需要目標電芯 NTC 曲線才能定案（見 §9）。
**EVT 硬性要求：`BIN` 不得直接短接到 VDD 或 VSS，且不得浮空。** 預留 10 kΩ 下拉焊位作為 NTC 未接時的合法終接。

### 7.7 MAX98357A `SD_MODE` 分壓（絕對最大值安全解）

**[手]** 絕對最大值：`VDD`／`LRCLK`／`BCLK`／`DIN` 對 GND 為 −0.3 … +6 V；
**「All Other Pins to GND −0.3 V to (VDD + 0.3 V)」** —— `SD_MODE` 屬後者。

本設計 `VDD` = `VSYS_AUDIO` = `VSYS_RAW`，其 NVDC min/max 尚未凍結；3.0 V 與 4.5 V 只作壓力點，
邏輯域為 3.3 V。→ 在受控最小 `SYS` 低於邏輯域時，若由 3V3 邏輯直驅 `SD_MODE` 會逼近或超過 `VDD` + 0.3 V。

數據手冊對此有明文 **[手]**：「若 `VDD` < 3.0 V 而 `VDDIO` = 3.3 V，必須在 `SD_MODE` 串約 2 kΩ 限流」，並註明
「使用 right channel 或 (left/2 + right/2) 模式時無此顧慮」。

**WP4 解法：`SD_MODE` 經 10 kΩ 上拉到 `VSYS_AUDIO` 本身，選 Left channel 模式。**

內部下拉 `RPD` = 92 / 100 / 108 kΩ **[手]**；判別門檻 `B2` = 1.245 / 1.4 / **1.5** V **[手]**（> `B2` 為 Left）。

```text
VSD_MODE = VSYS_AUDIO × RPD / (RPD + 10 kΩ)                                   [算]

3.0 V 壓力點：RPD = 92 kΩ、上拉 10.1 kΩ → 3.0 × 92/102.1 = 2.703 V
              vs B2 MAX 1.5 V → 1.80× 情境裕度
4.5 V 壓力點：RPD = 108 kΩ、上拉 9.9 kΩ → 4.5 × 108/117.9 = 4.122 V
              且由同一 rail 分壓，結構上不超過 VDD；正式門仍以 WP3 受控 min/max 重算
```

此解的三個結構性優點：

1. `SD_MODE` 由 `VSYS_AUDIO` 自身分壓而來，**恆 ≤ `VDD`**，絕對最大值在全電壓範圍天然不可能違反；
2. `VSYS_AUDIO` 關斷 → `SD_MODE` = 0 → 功放進 shutdown，**且無任何反灌路徑**；
3. 不需要任何 GPIO（核心板 MCU GPIO 已 33/33 全滿）。

耗流 **[算]**：`VSYS_AUDIO` / (10 kΩ + `RPD`) ≈ 3.7 / 110 kΩ = **33.6 µA，僅音訊域開啟時**；深睡為 0（§4.1）。

**已評估並否決的替代方案**：上拉 634 kΩ 到 `3V3_AON` 取 (left/2 + right/2) 單聲道下混。
否決理由 **[算]**：`VSYS_AUDIO` 關斷時 `3V3_AON` 經 634 kΩ 與內部 100 kΩ 分壓，使 `SD_MODE` ≈ 0.45 V 而 `VDD` = 0，
**違反絕對最大值 0.3 V 上限**並形成反灌。單聲道下混改由韌體在 I²S 資料側完成（Left 聲道送已混音資料），
零硬體代價。

### 7.8 MAX98357A `GAIN_SLOT`：EVT 以可換件保留全部檔位

增益比較器門檻為 `VDD` 的比例 **[手]**，故增益檔由 `GAIN_SLOT` 接法決定：

| 接法 **[手]** | 增益 `AV` |
| --- | --- |
| GND 經 100 kΩ | 15 dB |
| **GND 直接** | **12 dB** |
| 未接 | 9 dB |
| `VDD` 直接 | 6 dB |
| `VDD` 經 100 kΩ | 3 dB |

`VSYS_RAW` 直供的滿幅輸出功率受電源電壓平方限制（power-tree.md §6.2 的 0.56–0.86 W 只是 3.0／3.7 V 壓力情境 **[算]**），
**提高增益不會提高最大輸出功率**，只讓削波發生在更低的數位電平。故最終增益是
[verification-matrix.md](verification-matrix.md) 的**聲學資格輸出**，不是 WP4 可凍結項。

**EVT 作法：`GAIN_SLOT` 預留三個焊位** —— 0 Ω 到 GND（裝，12 dB 基線）、100 kΩ 到 GND（DNP，15 dB）、
0 Ω 到 `VDD`（DNP，6 dB）。可在不改板的前提下掃增益，配合 65 dBA @30 cm 資格。

### 7.9 BQ25628E buck 電感與電容 **[算]**

**[手]** 建議工作條件：`LSW` 0.68 – 2.2 µH；`CVBUS` ≥1 µF；`CPMID` ≥10 µF；`CSYS` 20 – 500 µF；
`fS` = 1.5 MHz；`BTST` 47 nF ≥10 V；`REGN` 4.7 µF ≥10 V。

式 (4) **[手]**：`IRIPPLE = VIN × D × (1 − D) / (fS × L)`，`D = VBAT / VVBUS`；最大紋波在 `D` ≈ 0.5。

```text
最壞 D = 0.5、VIN = 5 V：VIN × D × (1−D) = 5 × 0.5 × 0.5 = 1.25

L = 1.0 µH → IRIPPLE = 1.25 / (1.5e6 × 1.0e-6) = 0.833 A
L = 2.2 µH → IRIPPLE = 1.25 / (1.5e6 × 2.2e-6) = 0.379 A
```

數據手冊建議紋波為最大充電電流的 **20 – 40 %** **[手]**。以 `ICHG` 上限 1.0 A（PRD 快充目標）：

| L | `IRIPPLE` **[算]** | 佔 1.0 A | 判定 |
| --- | --- | --- | --- |
| 1.0 µH | 0.833 A | 83 % | ❌ 遠超建議 |
| **2.2 µH** | **0.379 A** | **38 %** | ✅ 落在 20–40 % |

式 (3) **[手]**：`ISAT ≥ ICHG + ½ IRIPPLE` = 1.0 + 0.190 = **1.19 A** → 選 `ISAT` ≥ 1.5 A，**建議 ≥2 A**。

`CSYS` 降額檢查 **[算]**（電容 −50 %）：

| 方案 | 標稱 | 最壞有效 | vs `CSYS` MIN 20 µF | 判定 |
| --- | --- | --- | --- | --- |
| 1×22 µF | 22 µF | 11.0 µF | ❌ 不足 |
| **2×22 µF** | 44 µF | **22.0 µF** | ✅ |
| 1×47 µF | 47 µF | 23.5 µF | ✅ |

**採 2×22 µF**（較 1×47 µF 有更低等效 ESR／ESL，且與 `CO` 共用料號）。
⚠ 數據手冊的 20 – 500 µF 標註「without de-rating」**[手]**，本節仍按 −50 % 降額驗算為保守側。

`VSYS_RAW` 總電容 **[算]**：`CSYS` 2×22 µF + TPS63802 `CI` 22 µF（§3.1 採 E2）= 66 µF，
遠低於 `CSYS` MAX 500 µF ✅。兩組電容雖在同一軌，但分屬不同 IC 且各有就近佈局要求（見 WP7A），
**不得合併為單一位號**。

`CPMID` 耐壓 **[手]**：「25 V 或更高為佳（對 15 V 輸入）」。本設計輸入為 5 V USB，`VBUS` 絕對最大 26 V。
**採 ≥16 V 耐壓**以涵蓋 USB 瞬態，並在 §9 列為需與 ESD 防護一併複核項。

---

## 8. BQ27427 SHUTDOWN 喚醒後學習參數保留：查證結論

這是 WP4 被指定的具體查證任務（power-datasheet-calculations.md §7.5 末段、verification.md D1 記錄）。

### 8.1 SLUSEB5B **明文給出**的事實

| # | 章節 | 原文事實 **[手]** |
| --- | --- | --- |
| F1 | §7.2.1 Design Requirements | 出廠時三個預programmed化學檔案與 gauging 參數存於 **ROM**；**「Upon device reset, the contents of ROM are copied to associated volatile RAM-based data memory blocks.」** |
| F2 | §7.2.1 | **「For proper operation, all parameters in RAM-based data memory require initialization.」** 可由實驗室更新或**由主機下載參數** |
| F3 | §5.5 Supply Current | `ISD` SHUTDOWN 模式電流 0.6 µA typ，測試條件註明 **「(LDO regulator output disabled)」** |
| F4 | 引腳表 | `VDD` 為 **1.8 V 調節器輸出**，需 2.2 µF 去耦；**不得**用於供電其他器件 |
| F5 | §5.8 | `tPUCD` = 250 ms typ，定義為「Time delay from rising edge of REGIN to the **Active** state. **Includes firmware initialization time**」 |
| F6 | §5.8 | `tSHDN` ≤250 ms（SHUTDOWN 命令到 LDO 輸出停用）；`tSHUP` ≥10 µs（SHUTDOWN 中 GPOUT 低時間）；`tWUVDD` = 8 ms（GPOUT 上升緣到 VDD 標稱輸出） |
| F7 | §5.7 註 | 「If the device is commanded to SHUTDOWN via I2C with VBAT > `UVLOIT+`, a **wake-up rising edge trigger is required on GPOUT**」 |
| F8 | §6.4 Device Functional Modes | 四個模式 INITIALIZATION／NORMAL／SLEEP／SHUTDOWN；細節**指向 BQ27427 Technical Reference Manual** |
| F9 | §7.4.1 佈局 | 「If the host is not using the GPOUT functionality, connect GPOUT to a GPIO of the host. In cases where the device is in SHUTDOWN, toggling GPOUT wakes up the gauge」 |

### 8.2 SLUSEB5B **未給出**的事實

| # | 缺口 |
| --- | --- |
| G1 | **未明文說明** RAM-based data memory（含 Impedance Track 學習值）在 SHUTDOWN 期間是否保留 |
| G2 | 未說明學習值（`Qmax`、`Ra` 阻抗表）的儲存位置是 RAM 或非揮發區 |
| G3 | 未給 OCV 重測／重新學習的收斂時間 |
| G4 | 未給 SHUTDOWN 喚醒後主機必須重下載哪些參數的清單 |

### 8.3 結論

> **查證結論：SLUSEB5B 未明文記載 SHUTDOWN 喚醒後學習參數是否保留。**
> **但它明文記載了兩個足以構成強推論的架構事實：資料記憶體是揮發性 RAM（F1、F2），且 SHUTDOWN 停用產生
> 內部 1.8 V 數位電源的 LDO（F3、F4）。**

**架構推論（標記為推論，不是數據手冊陳述）**：LDO 輸出停用 → 內部數位核心失電 → 揮發性 RAM 內容遺失 →
喚醒後等同 reset，ROM 預設值被複製回 RAM，主機必須重新下載完整配置。F5 的 `tPUCD` 把 GPOUT 喚醒後到
Active 的延遲與「從 REGIN 上升緣」的上電延遲**用同一個 250 ms 與同一句「includes firmware initialization
time」描述**，進一步支持「SHUTDOWN 喚醒 ≡ 上電初始化」。

**此推論不得當作已驗證事實。** 依 PRD R5.2 與 implement.md §3.3 的「無可驗證模型時必須標記為數據手冊計算 +
台架驗證」原則，本項狀態為：**未確認，WP9 台架驗證**。

### 8.4 對 D1／D2 決策的影響：D1 被進一步強化

[power-tree.md](power-tree.md) §5.1 與 power-datasheet-calculations.md §7.3 把 D2 的代價記為
「失去深睡期間的荷電狀態追蹤」。若 §8.3 推論成立，D2 的真實代價**顯著大於該描述**：

| 代價項 | 既有記錄 | 若 §8.3 推論成立 |
| --- | --- | --- |
| 深睡期間荷電追蹤 | 失去 | 失去 |
| 喚醒後配置 | 未提及 | **每次喚醒需重下載化學檔案與全部 data memory 參數** |
| 學習值（`Qmax`／`Ra`） | 未提及 | **可能遺失，精度退回未學習狀態直到重新學習循環完成** |
| 喚醒延遲 | 未提及 | `tWUVDD` 8 ms + `tPUCD` 250 ms **[手]**，加上主機下載時間 |
| 韌體複雜度 | 未提及 | 需在每次喚醒路徑實作完整重初始化與失敗處理 |

**判定：D1（保持 SLEEP，目標放寬至 50 µA 上限）不需重新評估，且理由比原記錄更強。**
D2 省 8.4 µA 的代價可能是「每次喚醒都失去電量計精度基礎」，而非僅「深睡期間不追蹤」。
這與 PRD 明文要求（「不得以 ESP32 ADC 電壓粗估替代燃料計」、「輸出可驗證的荷電狀態」）方向相反。

### 8.5 ⚠ 附帶發現：電池更換必然觸發燃料計重初始化

即使採 D1（SLEEP 模式，RAM 由 `BAT` 供電保持），下列情境仍會使 BQ27427 完全失電並遺失 RAM：

| 情境 | 是否遺失 RAM |
| --- | --- |
| 深睡（SLEEP 模式，`BAT` 在位） | **不遺失**（LDO 仍工作） |
| BATFET ship mode | BQ27427 由 `BAT` 直供而非 `SYS`，**不遺失** |
| **電池包拔除（內部可維修更換）** | **遺失** |
| 電芯保護板切斷 | **遺失** |
| 電芯放電至 `UVLOIT−` 1.95 V **[手]** 以下 | **遺失**（LDO auto-shutdown） |

PRD 已凍結「內部可維修更換電池包」與「更換後燃料計重新資格」。本節為該要求提供器件級依據：
**電池更換後必須重新執行化學檔案配置與學習循環，這不是可選的售後步驟，而是燃料計恢復精度的必要條件。**

→ 必須寫入 WP8 的首次上電／調試作業指導與售後維修流程（implement.md §5 已列燃料計學習循環為 WP9 項目，
本節補上「每次電池更換都要重跑」這一條）。

### 8.6 WP9 台架驗證項（本節產出）

| # | 驗證項 | 通過判準 |
| --- | --- | --- |
| V1 | I²C 命令進入 SHUTDOWN，實測 `BAT` 電流 | 接近 `ISD` 0.6 µA typ **[手]** |
| V2 | P04 平時保持 input／released；刻意切成 TCA9535 push-pull output-low ≥`tSHUP` 10 µs，隨即切回 input，觀察 `FUEL_GPOUT` 喚醒 | 器件回到 Active、I²C 可通訊；全程從不 output-high 與 BQ27427 GPOUT 對打 |
| V3 | **喚醒後讀回 data memory 關鍵參數與學習值** | **判定是否保留；這是 §8.3 推論的直接驗證** |
| V4 | 喚醒後到可通訊的實測延遲 | 與 `tWUVDD` 8 ms + `tPUCD` 250 ms **[手]** 比對 |
| V5 | 電池拔除／重插後讀回配置 | 確認 §8.5 結論，並量測重新學習收斂時間 |

V3 是唯一能關閉 G1／G2 缺口的證據；若 TI Technical Reference Manual 可取得，應先以文件關閉再以台架複核。

### 8.7 BQ27427 BAT→SRX 高側載流門

SLUSEB5B **[手]**：內建 sense 7 mΩ；`ISRX` 長期 RMS 2.0 A，10% device utilization 的 peak RMS 3.5 A
（−40…+70 °C）。PACK+ 必須以星點接 `BAT`，全部充放電電流只由 `SRX` 進出 system；BAT Kelvin layout 是
量測幾何，不是另一條繞過 sense 的高流路徑。

本文件 §3.1 已知峰值 1.682 A **尚未含前光與 EPD HV**，也沒有 RMS duty profile，因此不能宣稱 2 A／3.5 A
門有餘裕。精確負載與充電工況定案後必須重算 RMS／peak，並在 WP9 雙向充放電量測 BAT-SRX 壓降、計量讀值與
溫升。任何 PACK+→charger/load 旁路、只畫 BAT 細 Kelvin 線、或未覆蓋充電方向，都使門失敗。

---

## 9. 本文件產生的未關閉項

| # | 未關閉項 | 阻擋來源 | 解除條件 |
| --- | --- | --- | --- |
| U1 | automatic PWM/PFM 的實際轉換與非 PWM `VFB` 精度未規範（§1.1） | 1.06 A 是峰值電感電流條件；`VFB` accuracy 只規範 PWM | WP9 以 `MODE`=LOW／HIGH 掃 VIN/負載並量測模式、直流精度與紋波 |
| U2 | XFL4015 reference candidate 的 exact suffix／orderable MPN、容差、溫度／電流降額、Isat 定義與 land pattern（§2.4） | TI 推薦表不能提供 supplier-controlled orderability／package qualification | 取得並複核供應商受控資料；此前不是凍結料號 |
| U3 | `CI`／`CO` 的容值 vs DC bias 曲線（§3.1） | 需精確料號規格 | 取得 Murata 料號 DC bias 曲線 |
| U4 | KILIM外推／RC效果與總USB源預算（§5.3） | 僅1.6A規範；本批旁路尚無足夠總餘量 | J201總輸入含全部旁路，上電／穩態／拔插／弱源與溫度實測≤500mA；只測BQ不關門 |
| U5 | L1 vs L3 最終選擇（§5.7） | 需 WP9 判定 L1 拔插不對稱風險是否可接受 | WP9 故障注入結果 |
| U6 | 超級電容精確料號、容量、漏電（§6.3／§6.4） | 料號未選定 | 依 §6.4 的 S1–S6 準則選型 |
| U7 | BQ27427 `BIN` 與充電器 `TS` 的 NTC 共用或分立（§7.6） | 目標電芯 NTC 曲線未凍結 | 電芯定案 |
| U8 | I²C 上拉精確阻值（§7.4） | 匯流排總電容取決於 FPC 長度（WP1） | WP1 + bring-up 實測上升緣 |
| U9 | BQ27427 I²C 1 MΩ 下拉是否裝件（§7.5 選項 P1） | 需 ship mode 實測 | WP9 |
| U10 | `GAIN_SLOT` 最終增益檔（§7.8） | 聲學資格輸出 | WP9 聲壓/失真實測 |
| U11 | BQ27427 SHUTDOWN 學習參數保留（§8.3） | 數據手冊未載，TRM 未取得 | TI TRM 或 WP9 台架項 V3 |
| U12 | TCA9535 編號 SCPS217 → **SCPS201E** | 已同步更正目前文件 | 關閉；guard 禁止舊編號回流 |
| U13 | BQ27427 BAT→SRX RMS／peak 載流（§8.7） | 前光／EPD HV／duty／精確電芯未定 | 重算後 WP9 雙向充放電量測，不超 2 A RMS／3.5 A peak 且無旁路 |

---

## 10. 計算結果總表

| # | 項目 | 結果 | 判定 |
| --- | --- | --- | --- |
| 1 | `VFB` 容差補轉錄 | ±1 %（**僅 PWM mode**） | ⚠ 關閉數值轉錄缺口；automatic/PFM 未規範（U1） |
| 2 | PWM 條件 VOUT 誤差窗口（±0.5 %） | 3.2394 … 3.4177 V | ⚠ 在 3.0–3.6 V 內，但不得外推到 automatic/PFM |
| 3 | 到絕對邊界的算術距離 | 上側 0.1823 V、下側 0.2394 V | ⚠ **不是** PFM 紋波預算或資格門；LOW／HIGH 皆須實測 |
| 4 | IPEAK（C2、L=0.376 µH） | 1.00 A 負載 → 1.4812 A | ✅ 對 `IPK` MIN 4 A 有 2.70× |
| 5 | 電感飽和裕度 | 1.00 A 負載 → 3.04× | ✅ 無衝突 |
| 6 | `CO` 22 µF 有效值 | 最壞 11.0 µF ≥ 7 µF | ✅ 1.57× |
| 7 | `CI` 取捨 | **採 E2：22 µF** | ✅ 裕度 1.25× → 2.75× |
| 8 | 深睡混合工程包絡（超級電容1–5µA／I²C下拉DNP） | 歷史36.45–40.45µA；當前USB差量後 **40.25–44.25µA** | ⚠ typ/估算/部分保守預算混合，非整板max；50µA門未過 |
| 9 | D1名義餘量 | 歷史9.55–13.55µA；當前 **5.75–9.75µA** | ⚠ §4.5指定稳態，未知負載與過渡仍未測 |
| 10 | TCA9535 standby 測試條件 | 兩個包絡條件 typ 都是 0.9 µA | ✅ **關閉 WP3 §7.4 疑慮** |
| 11 | TCA9535 資料手冊編號 | **SCPS201E** | ✅ 舊誤記已同步更正（U12 關閉） |
| 12 | RILIM的BQ分支500mA級候選 | 5.6k±1%外推398–496mA及1.2k+330nF RC | ⚠ 非保證窗口，更不是J201總源門通過；旁路須另計 |
| 13 | `IINDPM` POR = 3.2 A 且拔線重置 | 無法提供安全默認 | 🔴 `RILIM` 升為**必裝安全元件** |
| 14 | 500 mA 硬體默認 vs 1 A 電池充電 | 固定 `RILIM` **不能同時滿足** | 🔴 **衝突一** → 採 L1 + DNP 預留 L3 |
| 15 | L1 拔插不對稱 | `IINDPM` 重置但 `EN_EXTILIM` 不重置 | ⚠ 韌體契約 + WP9 故障注入 |
| 16 | 超級電容漏電未計入深睡 | power-tree.md §5 缺此行 | 🔴 **衝突二** → 選型準則 S1 漏電 ≤5 µA |
| 17 | 超級電容容量 | 條件例8.32…474.97mF；LSM180nA指定條件 | ⚠ V_ready/全程負載/有效C未驗，不是選型保證 |
| 18 | RV-3028-C7 EEPROM／未用腳 | 37h：TCE/BSM 預設停用；35h：CLKOUT 預設 32.768 kHz；EVI 禁浮 | 🔴 產線寫入＋讀回 35h/37h；EVI 10 kΩ 上拉 |
| 19 | 後備切換模式 | **LSM（`BSM`=11）** | ✅ 維持既定模式；DSM接近後備電壓的風險來自條件模型，非已量得必然誤切換，見§6.7 |
| 20 | 24 h 保時精度 | ±1 ppm → ±0.086 s | ✅ 精度非本項門 |
| 21 | 上拉深睡貢獻 | 理想電阻高態無壓差，接口有限漏電仍須計 | ⚠ 不可全部忽略，USB指定穩態見§4.5 |
| 22 | TCA9535當前終接 | P10=10k／1% AON上拉BQ_PG；P16/P17=10k AON上拉CC；P15=100k下拉 | ⚠ 舊未分配下拉描述是歷史；PG專屬漏電資格另計 |
| 23 | I²C 上拉上界 | `RPU` ≤ 29.2 kΩ | ✅ 收窄未凍結範圍至約 2.2–10 kΩ |
| 24 | BQ27427 I²C 浮空防護 | 1 MΩ 下拉，**DNP**（P1） | ⚠ 裝件則 +6.6 µA |
| 25 | `SD_MODE` 絕對最大值 | 上拉至 `VSYS_AUDIO` 10 kΩ | ✅ 天然不可能違反；否決 `3V3_AON` 上拉 |
| 26 | `GAIN_SLOT` | EVT 三焊位可換件 | ✅ 最終增益屬 WP9 輸出 |
| 27 | BQ25628E Pin 16 `SW` → output inductor | **2.2 µH**、`ISAT` ≥ 2 A | ✅ 紋波 38 % 落在 20–40 % |
| 28 | `CSYS` 降額 | **2×22 µF** | ✅ 最壞 22.0 µF ≥ 20 µF |
| 29 | BQ27427 SHUTDOWN 保留 | **數據手冊未載**；架構推論為不保留 | ⚠ 未確認（U11）；**D1 理由被強化** |
| 30 | 電池更換 → 燃料計 RAM | 必然遺失 | ⚠ 更換後必須重跑化學檔案與學習循環 |
| 31 | BQ27427 BAT→SRX 載流 | 2 A RMS／3.5 A peak 器件界；已知 1.682 A peak 尚不完整 | ⚠ U13；禁止旁路，待完整負載重算與雙向台架 |

---

## 11. 邊界聲明

本文件是**數據手冊計算**，不是仿真結果，也不是實測結果。全部 **[算]** 值依 §0 的假設與 WP3 §0.1 的
A1–A5 推導；假設變更則結論必須重算。

本文件**不宣稱**下列任一項已通過資格門：`3V3_AON` 紋波／效率／暫態／熱／深睡電流、充電安全性、
500 mA 或 1 A 充電電流、24 小時 RTC 保時、聲壓或音訊失真、BQ27427 SHUTDOWN 行為。§5 與 §6 明確記錄
**兩個新發現的衝突**及其取捨；§8 明確記錄查證結論為**數據手冊未載**。

不含任何認證聲明，不含任何未實測的續航、聲學或效能承諾。所有 **[估]** 值（尤其 §6 的超級電容漏電三檔）
只用於建立選型條件，**不得**作為規格或採購依據。
