Panda-Intelligence/panda-standard-board/docs/design/power-datasheet-calculations.md

# Panda 標準電子書板：`3V3_AON` 數據手冊計算

工作包：WP3（核心電源／信號仿真與軟體驗證基線）
日期：2026-08-10
狀態：計算基線；§4.3 電感容差與 §7 FB 分壓衝突仍有效；**§6 對 1.06 A 的模式解讀已撤回並更正**；
官方模型模擬與原廠 EVM／受控 bench fallback 均未完成，故仍阻塞 schematic placement／WP4 pass

本文件只是 `3V3_AON` 的**數據手冊計算輸入**，不是資格主體或通過證據。PRD R5.2 的回退路線要求在
schematic placement 前完成原廠 EVM／受控 bench fallback；目前尚未執行。全部 TPS63802 數字直接引用
[tps63802-datasheet-parameters.md](tps63802-datasheet-parameters.md)（SLVSEU9D），本文件不重新抓取數據手冊。

---

## 0. 標記與假設宣告

| 標記 | 意義 |
| --- | --- |
| **[手]** | 官方數據手冊值，可在文件號對應章節複核 |
| **[算]** | 由 **[手]** 值依本文件列出的算式推算 |
| **[假]** | **規劃假設**，未經實測，不得作為承諾 |

### 0.1 本文件使用的假設（全部明確標示）

| # | 假設 | 值 | 為何是假設 | 解除條件 |
| --- | --- | --- | --- | --- |
| A1 | 電池側壓力情境（**不是 `VSYS_RAW` bounds**） | 3.0 V／4.2 V | 精確電芯、BQ25628E `VSYSMIN`／模式／load／DPM／thermal／BATFET／dropout 均未受控；TPS63802 實際 VIN 是 NVDC `SYS`，不能把電芯端情境直接當 rail min/max | WP3 由受控 charger／cell configuration 導出 `VSYS_RAW` min/max |
| A2 | 效率 η | 0.90 | 數據手冊式 (2) 允許「用效率曲線值，或假設 0.9」**[手]**。本文件無實測效率曲線 | EVM／台架效率掃描 |
| A3 | `3V3_AON` 最壞併發負載（已知項） | 0.70 A | MCU ≥0.5 A **[手]** + microSD 寫入峰值 0.2 A **[估]**（[power-tree.md](power-tree.md) §6.1，無官方統一值） | WP9 SD 實測 |
| A4 | `3V3_AON` 最壞併發負載（含 WP1 保留） | 1.00 A | A3 + 0.30 A 保留給 EPD 邏輯與觸控（**WP1 未交付，此 0.30 A 是保留額度而非實測值**） | WP1 面板／觸控資料 |
| A5 | boost 區開關頻率 | 1.4 MHz | 數據手冊只給三個無載、`MODE`=HIGH 測試點：boost@2.3 V=2.1 MHz、buck-boost@3.3 V=1.4 MHz、buck@4.3 V=1.6 MHz **[手]**。VIN=3.0 V 無對應測試點；取 1.4 MHz 因**較低頻率給較大紋波、較大 IPEAK**，為保守側 | EVM 實測開關頻率 |

⚠ A5 的額外邊界：三個 `fSW` 值的測試條件是**無載且 `MODE`=HIGH（forced PWM）**。`MODE`=LOW 只啟用
automatic PWM/PFM；不能由輸出負載值直接判定當下模式。因此 §4 的 IPEAK 計算只作指定重載條件的保守選型，
automatic-mode 的實際切換與頻譜見 §6。

---

## 1. 工作模式判定

依式 (1) **[手]**：`D = (VOUT − VIN) / VOUT`，VOUT = 3.3 V。

| TPS63802 VIN 情境 | 身份 | `D` **[算]** | 條件式模式判定 |
| --- | --- | --- | --- |
| 3.0 V | 壓力點 **[假 A1]** | +0.0909 | 若受控 `VSYS_RAW` 到此點則為 **boost** |
| 3.3 V | 交越壓力點 | 0.0000 | buck-boost 交越 |
| 3.6 V | 壓力點 | −0.0909 | buck |
| 4.2 V | 壓力點 **[假 A1]** | −0.2727 | buck |

**條件式判定：只有當受控 `VSYS_RAW < 3.3 V` 時才進入 boost。** 上表不代表 BQ25628E NVDC 已保證
3.0–4.2 V；實際 `SYS` bounds 必須由 WP3 受控 charger／cell configuration 取得。

### 1.1 交越點的位置意義

`D = 0` 的算術點在 3.3 V，但裝置是否、何時與多久經過此點取決於尚未受控的 NVDC `SYS`。數據手冊**未給**交越門檻的實際數值、
遲滯寬度或模式抖動規格，只給三個 `fSW` 測試點。因此：

- **不能**從數據手冊推導交越是否穩定、是否有模式抖動、抖動是否產生可聞或可測擾動；
- 交越行為列為**最高優先台架項**（[verification-matrix.md](verification-matrix.md) §4）。

---

## 2. 輸出能力包絡檢查

數據手冊 **[手]**：`VI ≥ 2.3 V` 且 VOUT = 3.3 V 時具備 **2 A** 輸出能力。

| 檢查 | 結果 |
| --- | --- |
| 3.0 V 壓力點是否 ≥ 2.3 V | 條件式是；**不能**外推成完整 `VSYS_RAW` 範圍已通過 |
| 2 A 能力是否覆蓋受控 NVDC min | **未判定**；`VSYS_RAW` min 未由 WP3 導出 |
| 啟動門檻 VIN >1.8 V **[手]** 是否覆蓋受控 NVDC min | **未判定**；3.0 V 只是一個壓力點 |

### 2.1 最壞併發負載 vs 2 A 包絡

| 情境 | 負載 | 佔 2 A 比例 **[算]** | 判定 |
| --- | --- | --- | --- |
| 已知項（MCU + SD） | 0.70 A **[假 A3]** | 35 % | ✅ 在包絡內 |
| 含 WP1 保留（+ EPD 邏輯 + 觸控） | 1.00 A **[假 A4]** | 50 % | ✅ 在包絡內，餘 50 % |

**判定：只有在 VIN≥2.3 V 的指定壓力情境下，1.00 A 假設負載佔 2 A 額定的 50%。這不是完整 NVDC 包絡通過；
在 WP3 取得受控 `VSYS_RAW` min/max 並完成官方模型模擬或 EVM／bench fallback 前，能力門保持阻塞。**

2 A 是指定輸入條件下的數據手冊**電流能力**上限，也不是熱能力上限。VSON-HR 10-pin、3.0 × 2.0 mm、方案面積
21.5 mm² **[手]** 的封裝在高負載下的溫升未計算（需損耗模型與熱阻，兩者皆非本文件可得），列為台架項。

---

## 3. boost 區電池側電流放大

boost 時輸入電流大於輸出電流。以式 (2) 的 DC 項推導放大係數 **[算]**：

```text
I_in / I_out = 1 / (η × (1 − D))
```

| VIN | `D` | 放大係數 **[算]**（η = 0.90 **[假 A2]**） |
| --- | --- | --- |
| 3.0 V | 0.0909 | **1.222×** |
| 3.3 V | 0.0000 | 1.111×（此處為交越，公式僅作連續性參考） |

### 3.1 3.0 V 壓力情境的 `VSYS_RAW` 峰值 **[算]**（不是最壞 rail bound）

```text
3V3_AON 輸出 1.00 A [假 A4] @ VIN 3.0 V
  → VSYS_RAW 抽取 1.00 × 1.222 = 1.222 A
+ 音訊峰值 0.46 A（[power-tree.md] §6.2，8 Ω @3.7 V [算]）
  → 1.682 A
```

⚠ 此 1.682 A 只是 3.0 V／η=0.90／假設負載組合的壓力情境，且**不含** adapter 前光
（`VSYS_FL_SW`，input=`VSYS_FL_IN`）與 EPD 高壓域（`EPD_HV_IN`，WP1 未交付）。它不是已導出的最壞總峰值。

**必須在下列項目定案後複算並比對**：
1. 目標電芯的持續／脈衝放電能力（電芯未凍結）；
2. 電池連接器與線束額定電流（[interfaces-and-connectors.md](interfaces-and-connectors.md)，料號未凍結）；
3. `MB1` 電流量測斷點的 0 Ω 封裝額定（[test-points.md](test-points.md) §2.2 已標此約束）；
4. BQ25628E SYS 輸出能力與 DPM 行為。

本文件不宣稱 1.682 A 可被滿足——這是**傳遞給電芯與連接器選型的輸入條件**，不是已通過的檢查。

---

## 4. 峰值電感電流與電感選型

### 4.1 式 (2) 代入

數據手冊 **[手]** 明確要求：「此計算必須以 boost mode 的**最小輸入電壓**進行」。故暫以 VIN = 3.0 V 壓力點 **[假 A1]**、
D = 0.0909、η = 0.90 **[假 A2]**。

```text
IPEAK = Iout / (η × (1 − D))  +  (Vin × D) / (2 × f × L)
        └──── DC 項 ────┘        └──── 紋波項 ────┘
```

代入 f = 1.4 MHz **[假 A5]**、L = 0.37 µH（數據手冊有效電感 MIN **[手]**）：

| Iout | DC 項 **[算]** | 紋波項 **[算]** | **IPEAK** **[算]** | ×1.2（數據手冊建議飽和裕度 **[手]**） |
| --- | --- | --- | --- | --- |
| 0.70 A **[假 A3]** | 0.856 A | 0.263 A | **1.119 A** | 1.343 A |
| 1.00 A **[假 A4]** | 1.222 A | 0.263 A | **1.485 A** | 1.783 A |
| 2.00 A（數據手冊上限） | 2.444 A | 0.263 A | **2.708 A** | 3.249 A |

以更悲觀的 L = 0.329 µH（0.47 µH 標稱經 −30% 降額，見 §4.3）：

| Iout | 紋波項 **[算]** | **IPEAK** **[算]** | ×1.2 |
| --- | --- | --- | --- |
| 0.70 A | 0.296 A | 1.152 A | 1.382 A |
| 1.00 A | 0.296 A | 1.518 A | 1.822 A |
| 2.00 A | 0.296 A | 2.741 A | **3.289 A** |

以 f = 2.1 MHz（若實測開關頻率較高）紋波項降至 0.176–0.197 A，IPEAK 隨之下降，故 §4.1 的表為保守側。

### 4.2 對 IC 峰值電流限制的比對

數據手冊 **[手]** boost mode `IPK`：MIN **4 A** / TYP 5 A / MAX 5.75 A。
**依數據手冊參數文件指示，選型以 MIN 4 A 為保守邊界，不用 TYP。**

| 情境 | IPEAK **[算]** | vs `IPK` MIN 4 A | 裕度 **[算]** |
| --- | --- | --- | --- |
| 0.70 A 負載 **[假 A3]** | 1.152 A（最悲觀） | 4 A | **3.47×** |
| 1.00 A 負載 **[假 A4]** | 1.518 A（最悲觀） | 4 A | **2.64×** |
| 2.00 A 數據手冊上限 | 2.741 A（最悲觀） | 4 A | **1.46×** |

**判定：全部情境的 IPEAK 都低於 `IPK` MIN 4 A。IC 限流不構成邊界。無衝突。**

### 4.3 🔴 衝突一：電感容差與建議工作條件的算術矛盾

數據手冊同時給出兩組互相衝突的約束 **[手]**：

| 來源 | 約束 |
| --- | --- |
| 建議工作條件 | **有效**電感 MIN 0.37 / NOM 0.47 / MAX 0.57 µH |
| 降額假設 | 電感有效值可變動 **+20% / −30%** |

若把降額直接疊在標稱值上求可行的標稱窗口 **[算]**：

```text
要讓 −30% 後仍 ≥ 0.37 µH  →  標稱 ≥ 0.37 / 0.70 = 0.529 µH
要讓 +20% 後仍 ≤ 0.57 µH  →  標稱 ≤ 0.57 / 1.20 = 0.475 µH
                              ────────────────────────────
                              0.529 > 0.475  →  無解
```

**算術上無任何標稱值同時滿足兩條。** 標稱 0.47 µH 經 −30% 得 0.329 µH，**低於**建議工作條件的 0.37 µH 下限，
而 0.47 µH 正是數據手冊自己的推薦料號值與典型應用值。

#### 取捨選項（不自行調整假設把數字湊進去）

| 選項 | 作法 | 代價／風險 |
| --- | --- | --- |
| **C1** | 判定「+20%/−30%」是**濾波組合矩陣的容許變動範圍**（即該範圍內組合仍有效），而建議工作條件的 MIN/MAX 已是**含容差後的有效值窗口**，兩者不應相乘 | 這是對數據手冊文義的**解讀**，非明文；必須在 WP4 以 TI 技術支援或 EVM 行為確認 |
| **C2** | 選 **±20%（或更緊）容差**的 0.47 µH 電感，使有效值 0.376–0.564 µH 完整落入 0.37–0.57 µH **[算]** | 排除 −30% 容差料；縮小可選料號池。**本文件建議此路線** |
| **C3** | 選標稱 0.50 µH ±15%（有效 0.425–0.575 µH）**[算]** | 0.57 上界僅剩 0.005 µH 裕度；且 0.50 µH 不在數據手冊推薦料號表內 |

**建議：C2。** 可行性驗算 **[算]**：

| 容差 | 標稱可行窗口 | 0.47 µH 是否落入 |
| --- | --- | --- |
| −30% / +20%（數據手冊降額） | ≥0.529 且 ≤0.475 µH | **無解** |
| ±20% | ≥0.462 且 ≤0.475 µH | ✅ 落入 |
| ±15% | ≥0.435 且 ≤0.496 µH | ✅ 落入 |

WP4 必辦：取得精確電感料號的**電流降額曲線與容差規格**，確認在 Panda 的最壞 DC 偏置電流與溫度下有效值
仍 ≥ 0.37 µH。**推薦料號表本身不構成此驗證**。

### 4.4 ⚠ 殘留風險：電感飽和先於 IC 限流

數據手冊推薦表 reference **[手]**：`XFL4015-471ME` 列 Isat 5.4 A、`DFE201612E` 列 Isat 5.5 A。
前者的 exact suffix／orderable MPN、容差、降額、Isat 定義與 land pattern 尚未由 supplier-controlled data 資格化。
IC boost `IPK` MAX 5.75 A **[手]**。

```text
Isat 5.4 / 5.5 A  <  IPK MAX 5.75 A
```

→ 故障或啟動暫態下，**電感可能在 IC 限流動作前先飽和**。

| 緩解因素 | 說明 |
| --- | --- |
| 正常工作 IPEAK 遠低於 Isat | 1.00 A 負載時 ×1.2 後 1.822 A，對 5.4 A 有 **2.96×** 裕度 **[算]** |
| 軟啟動斜坡 224 µs **[手]** | 限制啟動電流上升率 |
| 這是 TI 自己的推薦組合 | 表示 TI 接受此關係 |

**判定：記錄為已知殘留風險，非阻塞。** 但必須列入台架故障注入項（輸出短路、啟動至滿載），並在 WP4
確認所選料號的**飽和定義**（−20% 或 −30% 電感跌落點，各廠定義不同）。

---

## 5. 反饋分壓設計（式 3）

數據手冊 **[手]**：`R1 = R2 × (VOUT / VFB − 1)`，`VFB` = 500 mV，**R2 不得超過 100 kΩ**，
`IFB` typ 5 nA / **max 100 nA**。

### 5.1 阻值選擇 **[算]**

```text
VOUT / VFB − 1 = 3.3 / 0.5 − 1 = 5.6
```

| 選項 | R2 | R1 **[算]** | 標準值 | 分壓靜態電流 **[算]** |
| --- | --- | --- | --- | --- |
| **F1** | 100 kΩ（數據手冊上限） | 560 kΩ | ✅ 兩者皆 E24 | **5.00 µA** |
| F2 | 10 kΩ | 56 kΩ | ✅ 兩者皆 E24 | **50.00 µA** |
| F3 | 50 kΩ | 280 kΩ | ✅ E24 | 10.00 µA |

`R1/R2 = 5.6000` 精確，標稱輸出 **3.3000 V**。

### 5.2 `IFB` 誤差項 **[算]**

`IFB` 流入 FB 腳，抬高輸出：

```text
VOUT = VFB × (1 + R1/R2) + IFB × R1
```

| 選項 | `IFB` typ 5 nA | `IFB` max 100 nA |
| --- | --- | --- |
| F1（R1 = 560 kΩ） | 3.3028 V（+0.085 %） | **3.3560 V（+1.697 %）** |
| F2（R1 = 56 kΩ） | 3.3003 V（+0.008 %） | 3.3056 V（+0.170 %） |

**F1 的 `IFB` max 誤差達 +1.70 %，是本設計最大的單項直流誤差來源。**

### 5.3 電阻容差疊加 **[算]**

最壞高側 = R1 取上限、R2 取下限、`IFB` 取 max：

| 電阻容差 | VOUT_DC 窗口 **[算]** | 對 3.6 V 上界裕度 | 對 3.0 V 下界裕度 |
| --- | --- | --- | --- |
| ±1 % | 3.2446 … **3.4131 V**（−1.68 % … +3.43 %） | 0.187 V | 0.245 V |
| **±0.5 %** | 3.2721 … **3.3844 V** | **0.216 V** | **0.272 V** |
| ±0.25 % | 3.2860 … 3.3702 V | 0.230 V | 0.286 V |

比對基準 **[手]**：ESP32-S3 `VDD3P3` / `VDD3P3_RTC` / `VDD3P3_CPU` 建議輸入 **3.0 / 3.3 / 3.6 V**
（晶片規格書 v2.2；硬體設計指南另述 `VDD3P3_CPU`／`VDD3P3_RTC` 工作範圍 3.0–3.6 V）。

**⚠ 關鍵推論：直流設定誤差直接吃掉紋波與暫態預算。** ±1 % 電阻時最壞高側 3.4131 V，僅剩 **0.187 V**
給過衝 + 紋波；±0.5 % 時剩 0.216 V。

**建議：F1 + ±0.5 % 電阻。** 理由見 §7（F2 的 50 µA 分壓電流會直接摧毀深睡預算）。

### 5.4 ❗ 缺失輸入：`VFB` 容差未轉錄

[tps63802-datasheet-parameters.md](tps63802-datasheet-parameters.md) §3.3 只記錄 `VFB` **標稱 500 mV**，
未記錄其容差（±%／±mV）。

→ **§5.3 的誤差窗口尚未完整**：真實 VOUT_DC 窗口 = 電阻容差 × `IFB` × **`VFB` 容差**三項疊加。
WP4 必須從 SLVSEU9D 補轉錄 `VFB` 的 MIN/MAX 並重算本節。**本文件不宣稱 §5.3 是完整誤差預算。**

---

## 6. 更正：1.06 A 不是輸出負載的 PFM／PWM 切換點

SLVSEU9D 電氣特性表的完整參數名稱是 **“Peak Inductor Current to enter PFM-Mode”**：
`IPWM/PFM` = 1.06 A，條件 VIN=3.6 V、VOUT=3.3 V。它描述**峰值電感電流**，不是 `IOUT`。
先前把整板 0.70／1.00 A 輸出負載直接與 1.06 A 比較，並據此斷言「全部正常工作均為 PFM」，量綱與物理映射
都不成立；該判定及其「PWM 只在輸出超過 1.06 A 才出現」結論在本輪正式撤回。

### 6.1 可成立的器件事實

| `MODE` | 可成立的結論 | 不能推導的結論 |
| --- | --- | --- |
| LOW | 啟用 automatic PWM/PFM，以低輸出電流時允許 PFM 提升效率 | 不能只用 `IOUT < 1.06 A` 判定 PFM；輸出電流與峰值電感電流映射取決於 VIN、工作區、紋波與效率 |
| HIGH | 不論輸出電流均 forced PWM，以降低輸出紋波 | 不代表 automatic mode 在同一負載一定為 PFM |

深睡時為取得 11 µA typ Iq，`MODE` 必須可確定為 LOW；**活動狀態的最終 MODE 接法／控制策略尚未凍結**。
EVT 仍需保留 LOW／HIGH 的受控選擇能力，但這是量測手段，不是任何模式或紋波已合格的證明。

### 6.2 撤回的資格推論

- §5.3 的電壓窗口只在資料手冊明列的 **PWM-mode `VFB` accuracy** 條件下成立；不得外推成 PFM 直流窗口；
- 舊上側 0.216 V／下側 0.272 V 只能表示「未含 `VFB` 模式限制時的算術距離」，不得當作 automatic/PFM
  紋波資格預算；
- 現有文件與工具沒有證明 0.70 A、1.00 A 或任何正常負載的實際模式。

### 6.3 必辦動作

1. `MODE`=LOW 時，對 VIN=3.0／3.3／3.6／4.2／5.0 V 與 1 mA–2 A 負載掃描，從 SW／電感電流波形記錄
   automatic PWM/PFM 的實際轉換，而不是預先指定 1.06 A 輸出邊界；
2. 同條件以 `MODE`=HIGH 做 forced-PWM 對照；
3. 兩種模式均以 `VOUT` 全時域保持 3.0–3.6 V、PG 不誤動作與 Wi-Fi/SD 實際功能不退化為門；數據手冊未給
   獨立紋波 mV 規格，故不得用推導出的 0.1823／0.216 V 取代實測；
4. 若採可控 `MODE`，硬體必須保證復位與深睡時 LOW，且任何活動態 HIGH 策略須經上述掃描後才可凍結。

---

## 7. 🔴 衝突三：FB 分壓靜態電流與完整深睡包絡

舊基線漏計 FB 與 RTC 後備漏電，後續又曾錯把 VBUS-only TUSB320LI 計入電池深睡。同步修正後，F1 以外的
固定項（不含 FB）為 30.445 µA，RTC 後備漏電規劃包絡為 1–5 µA；USB 拔除時 U202 貢獻 0 µA。

### 7.1 重算 **[算]**

| 方案 | 分壓電流 | 固定項 + RTC 1–5 µA | vs 35 µA typ | vs 50 µA 上限 |
| --- | --- | --- | --- | --- |
| F1（R2 = 100 kΩ） | **+5.00 µA** | **36.45–40.45 µA** | ❌ 全包絡超標 | 餘 **9.55–13.55 µA** |
| F2（R2 = 10 kΩ） | +50.00 µA | 81.45–85.45 µA | ❌ | ❌ 超標 |
| F3（R2 = 50 kΩ） | +10.00 µA | 41.45–45.45 µA | ❌ | 餘 4.55–8.55 µA |

上述仍未包含 LSM6DSO32X power-down、4 顆負載開關與板級漏電實測，故 F1 **尚未通過** 50 µA 門。

### 7.2 不可迴避性

R2 = 100 kΩ 是**數據手冊明文上限** **[手]**，因此 5.00 µA 是此拓樸下分壓電流的**數學下限**，不能靠選更大
阻值降低。

```text
Idiv_min = VOUT / (R1 + R2) = 3.3 / (560k + 100k) = 5.00 µA
```

### 7.3 取捨選項（不調整假設把數字湊進去）

| 選項 | 節省 | 代價 | 判定 |
| --- | --- | --- | --- |
| **D1** 目標由 35 µA typ 放寬至以 50 µA 上限為準 | — | 36.45–40.45 µA + 尚未量得漏電必須全落在 50 µA；目前只剩 9.55–13.55 µA 計算餘裕 | ✅ 已決策；BQ27427 保持 SLEEP；**資格仍未通過** |
| **D2** BQ27427 深睡改 SHUTDOWN（0.6 µA）而非 SLEEP（9 µA） | 8.40 µA → 28.05–32.05 µA（仍未含待測項） | 失去深睡荷電追蹤；需 `FUEL_GPOUT` 喚醒，學習值保留未證實 | ❌ 未採用；若 D1 台架失敗才重評 |
| **D3** 改用 TPS631000（8 µA typ vs 11 µA） | 約 3.00 µA；若其餘假設不變則 33.45–37.45 µA | 分壓版本／可達電流未查證；2 A 條件 `VIN ≥3 V` 與 1S 截止重合 | 風險轉移，非淨改善 |
| **D4** 選漏電更低的負載開關 | 未知 | 需選型 | 無法量化 |

~~建議：D2 優先~~ **已裁決（2026-08-11）：採 D1。** 見 §7.5。

### 7.5 D1 決策理由（2026-08-11 用戶確認）

1. **自放電淹沒效應**：1S Li-Po 自放電約 2–3%/月，等效 **55–83 µA**，高於目前 36.45–40.45 µA 計算包絡；D2 每月只省約 0.3% 電量。
2. **用戶體驗代價不值**：普通「關機」= deep sleep（PRD 已凍結），意味著設備大部分時間處於深睡。D2 讓燃料計完全離線，每次喚醒的電量百分比都需重新估算，影響用戶體驗。
3. **目標本身需修正**：35 µA typ 是在不知道 FB 分壓有 5.00 µA 數學下限之前設定的。那 5 µA 是同步升降壓拓樸的架構成本（不可避免），目標漏算了必付項，修正目標比犧牲功能更合理。
4. **餘裕待證**：50 µA 上限目前只餘 **9.55–13.55 µA**，且 IMU、負載開關與板級漏電未實測；此數字只支持保留 D1 進 EVT，不構成通過。D3（TPS631000）仍屬風險轉移。

⚠ **BQ27427 從 SHUTDOWN 喚醒後學習參數保留情況與 OCV 重測收斂時間，須在 WP4 查 SLUSEB5B 原文確認。** 若日後實測顯示 D1 在 50 µA 上限下難以達標，再重評 D2。

### 7.6 附帶發現：TCA9535 standby 電流的測試條件不匹配

power-tree.md §5 引用 TCA9535 standby **0.9 µA typ / 4 µA max**，數據手冊測試條件為
**VCC = 3.6 V、輸入接地** **[手]**（SCPS201E）。

但本設計的擴充器輸入在深睡時**多路為 HIGH**（經上拉至 `3V3_AON`）：`FUEL_GPOUT`、`CHG_INT`、
`CHG_STAT`、`KEY_FN`、`SD_CD`、`PG_3V3_MAIN`（[gpio-budget.md](gpio-budget.md) §7）。

→ **0.9 µA typ 的測試條件與本設計實際狀態不符**，實際 standby 電流可能不同。列為 WP9 必測項，
不得以 0.9 µA 作為已確認值。

### 7.7 ✅ 反面查核：`PG` 上拉不吃深睡預算

`PG` 為 open-drain **[手]**，深睡時 TPS63802 正常工作 → `PG` 為高阻 → 上拉電阻**無電流**，僅擴充器輸入
漏電（±1 µA max，已含在 §7.4 的擴充器項）。

| 上拉阻值 | `PG` 拉低（故障）時電流 **[算]** | 深睡（`PG` 高）貢獻 |
| --- | --- | --- |
| 100 kΩ | 33.0 µA | ≈0（僅漏電） |
| 47 kΩ | 70.2 µA | ≈0 |
| 10 kΩ | 330.0 µA | ≈0 |

**判定：任務假設的「`PG` 上拉吃掉深睡餘裕」不成立。建議 100 kΩ**（故障電流低、對擴充器輸入閾值仍充裕）。
真正吃掉餘裕的是 §7.1 的 FB 分壓。

---

## 8. 有效電容 vs 標稱電容

數據手冊建議工作條件是**有效值** **[手]**；降額假設為電容 **+20% / −50%** **[手]**。

| 位置 | 數據手冊 MIN（有效） | 建議標稱 **[手]** | 最壞降額有效值 **[算]** | 判定 |
| --- | --- | --- | --- | --- |
| `CO` | **7 µF** | 22 µF 單顆（VOUT ≤ 3.6 V） | 11.0 µF | ✅ **1.57× 裕度** |
| `CI` | **4 µF** | 10 µF | 5.0 µF | ✅ **1.25× 裕度** |

若 `CO` 改 47 µF：最壞有效 23.5 µF，裕度 3.36×。

### 8.1 濾波組合合法性交叉檢查

數據手冊組合矩陣 **[手]**：0.47 µH 可搭 22 / 47 / 66 / 100 µF；**0.47 µH + 10 µF 不在允許組合內**。

⚠ **易誤讀點：該限制針對 `CO`（輸出電容），不是 `CI`（輸入電容）。** 本設計 `CO` = 22 µF（合法）、
`CI` = 10 µF（輸入電容表明文推薦值 **[手]**）。**兩者不衝突**，但 WP4 原理圖審查必須明確標注此區分，
避免複核者把 `CI` 誤判為非法組合。

### 8.2 ⚠ `CI` 裕度較緊 + DC bias 未計

`CI` 最壞裕度僅 **1.25×**，且數據手冊的 −50% 是**通用降額假設**，未針對本設計實際條件：

| 未計因素 | 影響 |
| --- | --- |
| 實際 DC bias | `VSYS_RAW` 上界尚未受控；4.5–5 V 只能作壓力情境。6.3 V 0603 X5R 在高偏置下的容值跌落**可能超過 50%**，須以 WP3 受控 max 重算 |
| 溫度特性 | X5R 為 ±15%（−55 至 +85 °C）；X7R 為 ±15%（−55 至 +125 °C） |
| 老化 | 陶瓷電容有老化率，數據手冊降額未明示是否已含 |

**WP4 必辦**：取得精確料號的**容值 vs DC bias 曲線**，在最壞偏置、溫度與老化後驗證有效值仍
≥ `CI` MIN 4 µF / `CO` MIN 7 µF。**推薦料號表不構成此驗證。**

可選緩解（WP4 取捨，本文件不凍結）：

| 選項 | 作法 | 代價 |
| --- | --- | --- |
| E1 | `CI` 改 10 V 耐壓（如 `GRM188R61A106ME69`，ESR 40 mΩ） | ESR 由 10 → 40 mΩ |
| E2 | `CI` 改 22 µF / 6.3 V（如 `GRM188R60J226MEA0`） | 佔位不變、成本略增；輸入電容值可無限制增加 **[手]** |
| E3 | 維持 10 µF / 6.3 V | 需 DC bias 曲線證明裕度足夠 |

另有硬性要求 **[手]**：若輸入源距 TPS63802 超過數英寸，需在陶瓷旁路外追加 bulk 電容（典型 47 µF 電解／鉭）。
本設計 `VSYS_RAW` 來自同板 BQ25628E，距離短，故**預期不需要**——但此判定須在 WP7A 實際佈局距離確定後複核。

---

## 9. `MODE` 腳在四個電源狀態的電平

硬體已凍結 `MODE` 接地（LOW = power save）（[power-tree.md](power-tree.md) §2.2）。本節記錄各狀態的
**要求**，供 §6.3 第 4 點的可控 `MODE` 選項評估：

| 狀態 | `3V3_AON` | 要求電平 | 理由 |
| --- | --- | --- | --- |
| 工廠運輸／長期倉儲 | 關（BATFET ship mode） | LOW（接地，天然滿足） | 軌已斷電，`MODE` 電平無效；接地確保不浮空 |
| **深睡眠** | 開 | **必須 LOW** | forced PWM 會大幅拉高輕載 Iq，直接摧毀 §7 預算 |
| 閱讀待機 | 開 | **待台架後凍結**；復位預設 LOW | 不能由輸出負載與 1.06 A 直接判定模式 |
| 螢幕刷新 | 開 | **待台架後凍結**；LOW／HIGH 都要量測 | 0.70–1.00 A 輸出負載不能直接映射到峰值電感電流條件 |

**判定：只有深睡 LOW 是已知必要條件；活動態策略未凍結。** 0 Ω 跳線／焊橋用於 LOW／HIGH 對照；
不得把保留跳線寫成 PFM 已知不合格時的唯一退路，也不得在實測前宣稱任一活動態模式正確。

---

## 10. 電感 DCR 損耗比較（推薦料號取捨）

以 Iout = 1.00 A **[假 A4]**、VIN = 3.0 V boost、I_L(rms) ≈ 1.222 A **[算]**（近似取 DC 項）：

| 料號 | DCR **[手]** | 尺寸 **[手]** | DCR 損耗 **[算]** | 佔 3.3 W 輸出 |
| --- | --- | --- | --- | --- |
| XFL4015 family reference（TI 表列 `XFL4015-471ME`，exact MPN 未資格化） | 7.6 mΩ（TI 表列） | **4.0 × 4.0 × 1.5 mm family body envelope**；land pattern 未凍結 | **11.3 mW** | 0.34 % |
| `DFE201612E` (Toko) | 26 mΩ | 2.0 × 1.6 × 1.2 mm | **38.8 mW** | 1.18 % |

**表列差異為 27.5 mW，約 0.8 個百分點；機械比較是 4.0×4.0×1.5 family body envelope vs
2.0×1.6×1.2 mm。**

此為 WP4／WP7A 的候選權衡輸入，不是精確料號推薦。路線 B 支持保留 XFL4015 family 作低 DCR reference，
但 exact suffix／orderable MPN、tolerance、derating、Isat definition 與 supplier-controlled land pattern 未關閉前，
不得寫成 EVT 採用件或建立凍結 footprint。

⚠ 此計算只含 DCR 導通損耗，**不含**：交流損耗（鐵損）、開關損耗、FET 導通損耗（高側 typ 47 mΩ **[手]**，
其餘 FET 阻值未轉錄）、閘極驅動與控制器損耗。**因此不得當作效率預測**，僅供兩顆推薦電感的相對比較。

---

## 11. 計算結果總表

| # | 項目 | 結果 | 判定 |
| --- | --- | --- | --- |
| 1 | 工作模式壓力點（3.0/3.3/3.6/4.2 V） | boost / 交越 / buck / buck（條件式） | ⚠ `VSYS_RAW` bounds 未凍結；列最高優先模型／台架項 |
| 2 | 2 A 額定 vs 1.00 A 假設負載 | VIN≥2.3 V 時為 50 % | ⚠ 只在指定條件成立；完整 NVDC 包絡未通過 |
| 3 | boost 壓力情境放大係數 | 1.222× @3.0 V | ⚠ 1.682 A 只是未含前光／EPD 的情境值，不是最壞 rail 結論 |
| 4 | IPEAK vs `IPK` MIN 4 A | 最壞 2.741 A @2 A 負載 | ✅ **無衝突，1.46× 裕度** |
| 5 | 電感容差 | 數據手冊兩條約束**算術無解** | 🔴 **衝突一** → 選 ±20 % 容差料（C2） |
| 6 | 電感 Isat vs `IPK` MAX | 5.4/5.5 A < 5.75 A | ⚠ 殘留風險，列故障注入台架項 |
| 7 | FB 分壓 R1/R2 | 560 kΩ / 100 kΩ，標稱 3.3000 V | ✅ 標準值精確 |
| 8 | `IFB` max 誤差 | +1.697 % | ⚠ 最大單項直流誤差 |
| 9 | 電阻容差疊加 | ±0.5 % → 3.2721…3.3844 V | ✅ 在 3.0–3.6 V 內，紋波預算 0.216/0.272 V |
| 10 | `VFB` 容差 | ±1%（只規範 PWM）已於 key-calculations 補轉錄 | ⚠ PWM 算術窗口可算；不得外推 automatic/PFM |
| 11 | `IPWM/PFM` 1.06 A | **峰值電感電流條件，不是輸出負載切換點** | ⚠ 舊「全部正常狀態為 PFM」結論已撤回；automatic-mode 轉換 + LOW/HIGH 紋波須台架量測 |
| 12 | 深睡 current baseline | 本文件初算 36.40 µA；後續修正含 RTC 1–5 µA、TUSB VBUS-only → 36.45–40.45 µA | ⚠ D1=50 µA 上限；仍缺 IMU／開關／板級實測 |
| 13 | `PG` 上拉深睡貢獻 | ≈0 | ✅ 任務假設的此項風險**不成立** |
| 14 | TCA9535 standby 測試條件 | 與本設計輸入狀態不符 | ⚠ 不得以 0.9 µA 為已確認值 |
| 15 | `CO` 22 µF 有效值 | 最壞 11.0 µF ≥ 7 µF | ✅ 1.57× |
| 16 | `CI` 10 µF 有效值 | 最壞 5.0 µF ≥ 4 µF | ⚠ 僅 1.25×，須 DC bias 曲線 |
| 17 | 0.47 µH + 10 µF 疑似非法 | 該限制針對 `CO`，`CI` 不受限 | ✅ 無衝突，但須在原理圖標注避免誤判 |
| 18 | `MODE` 四狀態電平 | 僅「螢幕刷新」有條件性 HIGH 需求 | ✅ 跳線保留正確 |
| 19 | 電感 DCR 損耗 | 11.3 vs 38.8 mW | 建議 EVT 用低 DCR 件（路線 B 一致） |

---

## 12. 傳遞給下游工作包的必辦項

| 工作包 | 必辦 |
| --- | --- |
| **使用者決策** | 衝突三 **✅ 已決策 D1（2026-08-11）** | — |
| **WP4** | 補轉錄 `VFB` 容差並重算 §5.3；取得電感容差／電流降額曲線（C2）；取得 `CI`／`CO` DC bias 曲線；選 ±0.5 % 分壓電阻；原理圖標注 `CI` vs `CO` 組合限制區分；`PG` 上拉建議 100 kΩ |
| **WP6A** | 數據手冊 Layout 要求（輸入輸出電容緊靠 IC、走線寬而直）進入預 Layout 檢查 |
| **WP7A** | 複核 `VSYS_RAW` 至 TPS63802 的實際距離是否需 bulk 電容（§8.2） |
| **WP9** | PFM 紋波（強制）、buck/boost 交越、負載階躍、啟動／關斷、效率、熱、深睡逐域電流、TCA9535 實際 standby、故障注入 |
| **電芯／連接器選型** | 保留 1.682 A 壓力情境（不含前光與 EPD HV）；待 WP3 受控 `VSYS_RAW` min/max 與 WP1 負載後重算真正包絡 |

---

## 13. 邊界聲明

本文件是數據手冊計算，**不是仿真結果，也不是實測結果**。全部 **[算]** 值依 §0.1 的假設推導；假設變更則
結論必須重算。本文件**不宣稱** `3V3_AON` 已通過任何資格門：紋波、效率、暫態、熱與深睡電流全部待
[verification-matrix.md](verification-matrix.md) §4 的台架實測。§7 明確記錄深睡預算**已超 35 µA typ 目標**，
本文件不宣稱達標。不含任何認證聲明，不含任何未實測的續航、聲學或效能承諾。
