Panda-Intelligence/panda-standard-board/hardware/thin18-compact/validate_split_c1.py

#!/usr/bin/env python3
"""Rebuild both native candidates, compare their CAD, and verify sourcing identities."""
from pathlib import Path
import argparse, hashlib, json, re, subprocess, sys, tempfile
import xml.etree.ElementTree as ET
from _split_c1_common import ROOT, REPO, REL, STEM, BASELINE_COMMIT, kicad_python, sha
from _split_c1_sourcing import geometry_digest, patch_block
from _core_c1_pcb_patch import copper
sys.path.insert(0, str(ROOT / "tools"))
from prune_core_c1_stubs import blocks

def canonical(text, pcb):
    if not pcb:
        return re.sub(r"\s+", " ", re.sub(r'\(uuid "[^"]+"\)', "", text)).strip()
    items = list(blocks(text, "(segment")) + list(blocks(text, "(via"))
    rest = text
    for start, end, _ in sorted(items, reverse=True):
        rest = rest[:start] + rest[end:]
    normalized = re.sub(r"\s+", " ", rest).strip()
    ordered = "\n".join(re.sub(r"\s+", " ", block).strip() for _, block in sorted(copper(text).items()))
    return normalized + "\n" + ordered

def counts(folder):
    drc = json.loads((folder / "verification/drc.json").read_text())
    erc = json.loads((folder / "verification/erc.json").read_text())
    result = {"drc": len(drc["violations"]), "open": len(drc["unconnected_items"]),
              "parity": len(drc["schematic_parity"]),
              "erc": sum(len(sheet["violations"]) for sheet in erc["sheets"])}
    if any(result.values()):
        raise ValueError("Native CAD gates failed: " + str(result))
    return result

def main():
    parser = argparse.ArgumentParser()
    parser.add_argument("--output", type=Path, default=ROOT / "split-c1-validation.json")
    args = parser.parse_args()
    subprocess.run([kicad_python(), str(ROOT / "verify_split_c1.py")], check=True)
    record = {"schema": "panda-split-c1-validation-v2", "replay_baseline_commit": BASELINE_COMMIT,
              "files": {}, "manufacturing_release": False}
    with tempfile.TemporaryDirectory(prefix="panda-split-c1-validation-") as temporary:
        for board, candidate, builder, relative in [
            ("Core-C1", "core-c1-96x68-split", "build_core_c1_split.py", REL / (STEM + ".kicad_pcb")),
            ("Display-C1", "display-c1-45x36-production-bom", "build_display_c1_production.py", Path("PANDA-EPD0426-SPI-EVT.kicad_pcb"))]:
            current = ROOT / candidate
            rebuilt = Path(temporary) / candidate
            subprocess.run([sys.executable, str(ROOT / builder), "--output", str(rebuilt)], check=True)
            paths = [current / relative] + sorted((current / relative).parent.glob("*.kicad_sch"))
            for path in paths:
                replay = rebuilt / path.relative_to(current)
                if canonical(path.read_text(), path.suffix == ".kicad_pcb") != canonical(replay.read_text(), path.suffix == ".kicad_pcb"):
                    raise ValueError("Rebuilt CAD differs: " + str(path.relative_to(REPO)))
                record["files"][str(path.relative_to(REPO))] = {
                    "sha256": sha(path), "non_property_cad_digest": geometry_digest(path.read_text()),
                    "rebuild_geometry_and_properties_equal": True,
                    "rebuild_comparison_note": "Schematic object UUIDs ignored; PCB segment/via order canonicalized with UUIDs retained."}
            record["files"][board] = {"native_checks": {"current": counts(current), "fresh_rebuild": counts(rebuilt)}}
    from verify_split_c1_power_integrity import inspect as inspect_power
    power=inspect_power(ROOT/'core-c1-96x68-split',ROOT/'core-c1-96x68-split/verification/netlist.xml')
    record['functional_power_contract_passed']=power['functional_pin_contract_passed']
    from verify_split_c1_hardware_finish import inspect as inspect_hardware
    finish=inspect_hardware(ROOT/'core-c1-96x68-split',ROOT/'core-c1-96x68-split/verification/netlist.xml')
    record['hardware_default_off_and_direct_shutdown_passed']=finish['default_off_topology_passed'] and finish['non_i2c_shutdown_path_present']
    from _split_c1_enclosure_study import openscad_study
    mechanical_inputs=json.loads((ROOT/'split-c1-mechanical-inputs.json').read_text())
    if (ROOT/'SPLIT-C1-ENCLOSURE-STUDY.scad').read_text()!=openscad_study(mechanical_inputs):
        raise ValueError('Stale side-battery OpenSCAD study')
    source_paths = [ROOT / name for name in [
        "audit_split_c1_assembly_process.py", "test_split_c1_assembly_process.py", "build_split_c1_process_entry.py",
        "_split_c1_cap_drill_eco.py", "verify_split_c1_cap_drill.py", "SPLIT-C1-CAP-DRILL.md", "split-c1-cap-drill-adoption.json",
        "_split_c1_fabrication.py", "split-c1-fabrication-contract.json", "build_split_c1_order_entry.py", "test_split_c1_fabrication.py", "verify_split_c1_fabrication.py",
        "_split_c1_hardware_finish_eco.py", "verify_split_c1_hardware_finish.py", "split-c1-hardware-finish.json", "split-c1-hardware-finish-layout.json", "split-c1-hardware-finish-adoption.json", "SPLIT-C1-HARDWARE-FINISH.md",
        "test_split_c1_control.py", "verify_split_c1_control.py", "split-c1-control-contract.json",
        "_split_c1_power_integrity_eco.py", "split-c1-power-integrity-layout.json", "split-c1-power-integrity.json", "SPLIT-C1-POWER-INTEGRITY.md", "SPLIT-C1-HANDOFF.md", "split-c1-power-integrity-adoption.json", "verify_split_c1_power_integrity.py", "test_split_c1_power_integrity.py", "_split_c1_common.py", "_split_c1_sourcing.py", "_split_c1_prototype_eco.py", "_split_c1_domestic_eco.py", "_split_c1_usb_eco.py", "_split_c1_switch_eco.py", "_split_c1_vbus_eco.py", "_split_c1_panel_eco.py", "_split_c1_microsd_eco.py", "_split_c1_mos_eco.py", "split-c1-mos-layout.json", "_split_c1_rtc_eco.py", "split-c1-rtc-layout.json", "split-c1-microsd-layout.json", "split-c1-candidate-review.json", "SPLIT-C1-PROCUREMENT-QUESTIONS.md", "_split_c1_esd_eco.py", "_split_c1_battery_eco.py", "_split_c1_land_guards.py", "_split_c1_enclosure_study.py", "SPLIT-C1-ENCLOSURE-STUDY.scad", "SPLIT-C1-PACK-INPUTS.md", "split-c1-jlc-catalog-observation.json", "split-c1-domestic-eco.json", "_core_c1_pcb_patch.py",
        "build_core_c1_split.py", "build_display_c1_production.py", "validate_split_c1.py",
        "verify_split_c1.py", "audit_split_c1_mechanical.py", "audit_split_c1_domestic.py",
        "split-c1-domestic-policy.json", "SPLIT-C1-DOMESTICIZATION.md", "C4D8-RTC-DECISION.md", "SPLIT-C1-RTC-FIRMWARE.md", "split-c1-smt-consignment.json", "split-c1-supply-plan.json", "verify_split_c1_supply.py", "SPLIT-C1-SUPPLY-REQUEST.md", "export_production.py",
        "export_jlc.py", "freeze_split_c1_release.py", "release_split_c1.py",
        "split-c1-sourcing-evidence.json", "core-c1-routing-closure.json",
        "package_jlc_prototype.py", "JLC-PROTOTYPE-HANDOFF.md",
        "split-c1-mechanical-inputs.json", "tools/prune_core_c1_stubs.py", "tools/verify_split_c1_land_controls.py",
        "qualification/c4d-evt/verify_qualification.py", "qualification/c4d-evt/run_negative_controls.py",
        "qualification/c4d-evt/qualification-plan.json"]]
    for candidate in ["core-c1-96x68-split", "display-c1-45x36-production-bom"]:
        source_paths.extend(p for p in (ROOT / candidate).rglob("*") if p.is_file()
                            and (p.suffix in {".kicad_mod", ".kicad_sym", ".kicad_pro", ".kicad_dru"}
                                 or p.name in {"fp-lib-table", "sym-lib-table"}))
    source_paths.extend(p for p in (REPO/"firmware/split_c1").rglob("*")
                        if p.is_file() and p.suffix in {".hpp", ".cpp", ".md"})
    for path in sorted(source_paths):
        record["files"].setdefault(str(path.relative_to(REPO)), {"sha256": sha(path)})
    evidence = json.loads((ROOT / "split-c1-sourcing-evidence.json").read_text())
    verified = 0
    for board, candidate in [("Core-C1", "core-c1-96x68-split"), ("Display-C1", "display-c1-45x36-production-bom")]:
        tree = ET.parse(ROOT / candidate / "verification/netlist.xml")
        components = {c.get("ref"): {f.get("name"): f.text or "" for f in c.findall("fields/field")}
                      for c in tree.findall("components/comp")}
        for row in evidence["entries"]+evidence.get("additive_entries",[]):
            if row["board"] != board:
                continue
            for ref in row["refs"]:
                fields = components[ref]
                for key in ["Manufacturer", "MPN", "LCSC"]:
                    expected = row[{"Manufacturer":"manufacturer", "MPN":"mpn", "LCSC":"library_id"}[key]]
                    if fields.get(key) != expected:
                        raise ValueError(f"Wrong purchasing identity: {board}/{ref}/{key}")
                verified += 1
    # A plug library ID must never be accepted for a socket.
    test = '(footprint "test" (property "Reference" "J601") (property "Manufacturer" "HCTL") (property "MPN" "HC-PBB40C-60DS-0.4V-1.5-02") (property "LCSC" "C19089235"))'
    socket = next(row for row in evidence["entries"] if row["board"] == "Core-C1" and "J601" in row["refs"])
    try:
        patch_block(test, "J601", socket, True)
    except ValueError:
        pass
    else:
        raise ValueError("Conflicting catalog ID was accepted")
    record.update(identity_verified_new_refs=verified, conflicting_part_id_rejection_checked=True,
                  native_all_60_pin_check_passed=True)
    args.output.write_text(json.dumps(record, indent=2) + "\n")
    print(json.dumps({"rebuilds_match": True, "identity_verified_refs": verified, "manufacturing_release": False}, indent=2))

if __name__ == "__main__":
    main()
