Panda-Intelligence/panda-standard-board/hardware/thin18-compact/_split_c1_battery_eco.py

"""HCTL HC-HY-2AWT primary 2.0mm/3A right-angle battery connector ECO."""
import json,re,uuid
from pathlib import Path
from _split_c1_sourcing import blocks,property_value
FP='panda-standard:HCTL_HC_HY_2AWT'
DOC='https://www.hctldz.com/static/upload/2025/10/17/202510175810.pdf'
DESCRIPTION='HCTL HC-HY-2AWT Rev.A primary p22: 2.0mm pitch,3A,250V,-40..105C. Signal lands1.2x3.80,anchors1.2x3.70,rows7.60mm. Height5.2mm nominal/+0.3 general tolerance. Pin1=BAT_CONN_P,pin2=GND,MP no-net. Housing/mate AWG26 polarity and mounted clearance require EVT. Connector rating does not certify the existing battery copper or pack for3A.'

def uid(k):return str(uuid.uuid5(uuid.NAMESPACE_URL,'panda/battery-hy/'+k))

def battery_geometry(fp):
    if property_value(fp,'Reference')!='J301':raise ValueError('Expected battery J301')
    pose=tuple(float(v or 0) for v in re.search(r'\(at\s+([-\d.]+)\s+([-\d.]+)(?:\s+([-\d.]+))?\)',fp).groups())
    if pose!=(49.75,23,0):raise ValueError('Battery pose predecessor differs')
    fp=re.sub(r'\(at\s+49\.75\s+23\)','(at 62 12 90)',fp,count=1)
    found=[]
    for a,b,p in reversed(list(blocks(fp,r'\(pad\s'))):
        n=re.match(r'\(pad\s+"([^"]+)"',p).group(1)
        xy=tuple(map(float,re.search(r'\(at\s+([-\d.]+)\s+([-\d.]+)',p).groups()))
        size=tuple(map(float,re.search(r'\(size\s+([-\d.]+)\s+([-\d.]+)',p).groups()))
        if n in ('1','2'):
            old=(-.6 if n=='1' else .6,-2.21)
            if xy!=old or size!=(.6,.65):raise ValueError('Battery signal predecessor differs')
            new=(-1 if n=='1' else 1,-2.21);newsize=(1.2,3.8)
        elif n=='MP':
            if abs(xy[0])!=2.025 or xy[1]!=1.495 or size!=(.85,1.34):raise ValueError('Battery anchor predecessor differs')
            new=(-3.2 if xy[0]<0 else 3.2,5.39);newsize=(1.2,3.7)
        else:raise ValueError('Unexpected battery pad')
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
